aeolyus/ha-green-poe-scad/renders/front.png

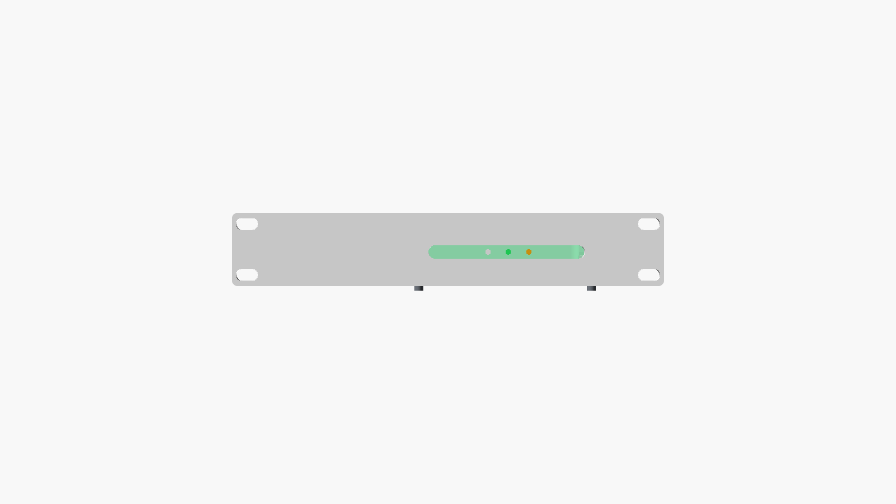
renders/front.png
