aeolyus/ha-green-poe-scad/renders/front_ethernet_far_right.png

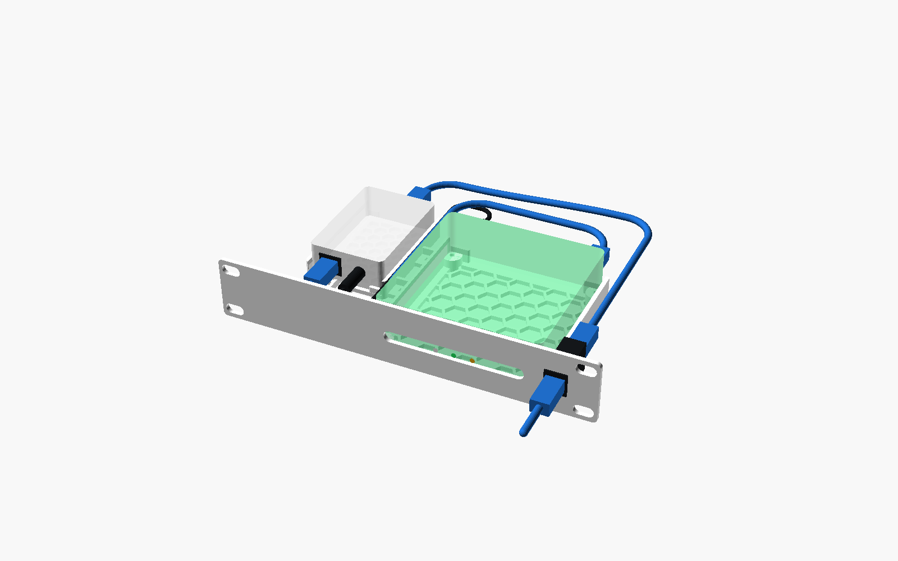
renders/front_ethernet_far_right.png
