aeolyus/ha-green-poe-scad/renders/x2d_plate.png

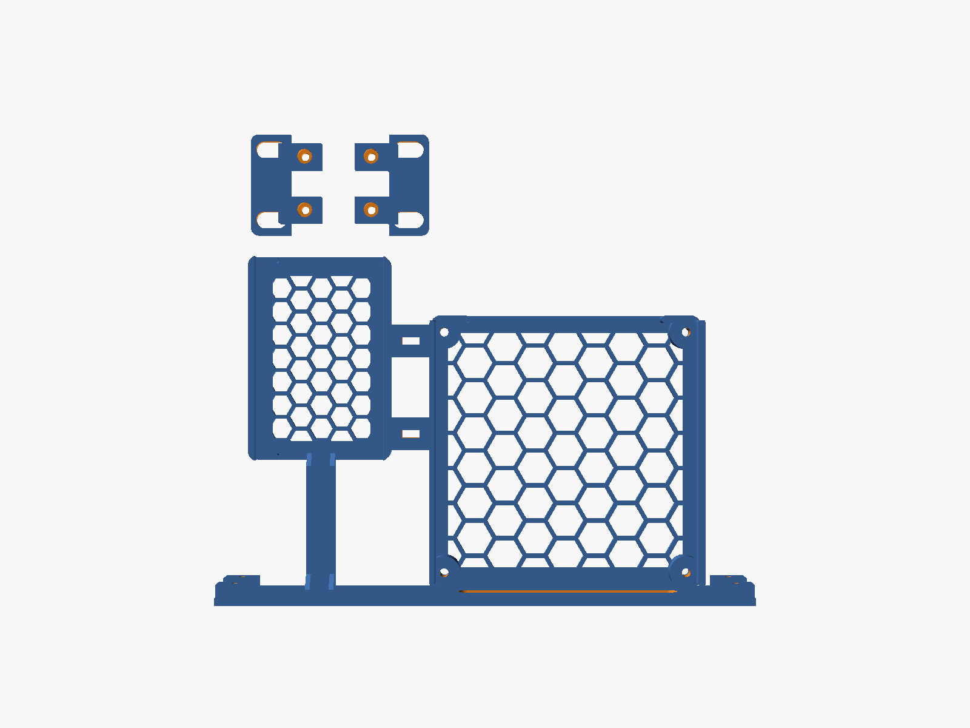
renders/x2d_plate.png
