aeolyus/ha-green-poe-scad/viewer/variants/stacked_center/viewer_led_activity.stl

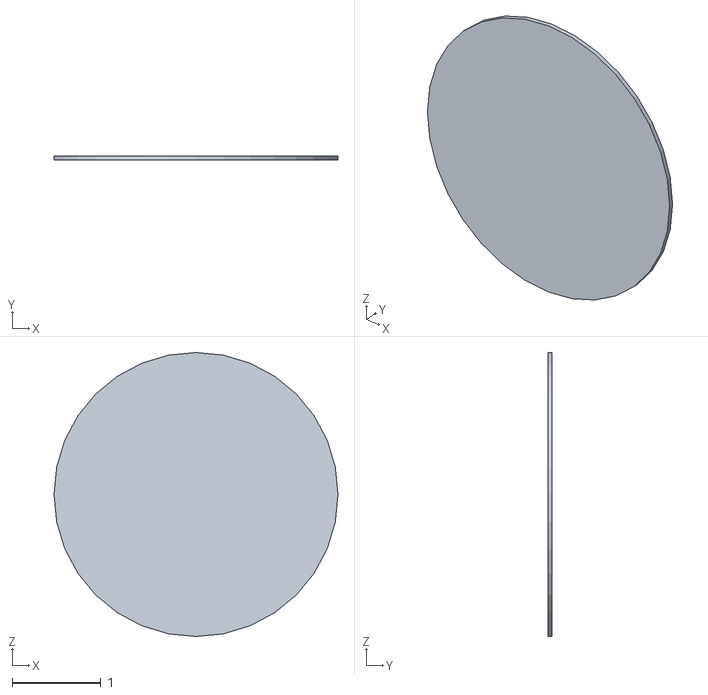
[picture p20: CAD file, 2026-08-29]
viewer/variants/stacked_center/viewer_led_activity.stl
3.20 x 0.05 x 3.20
