aeolyus/ha-green-poe-scad/viewer/viewer_retention_dovetail_gates.stl

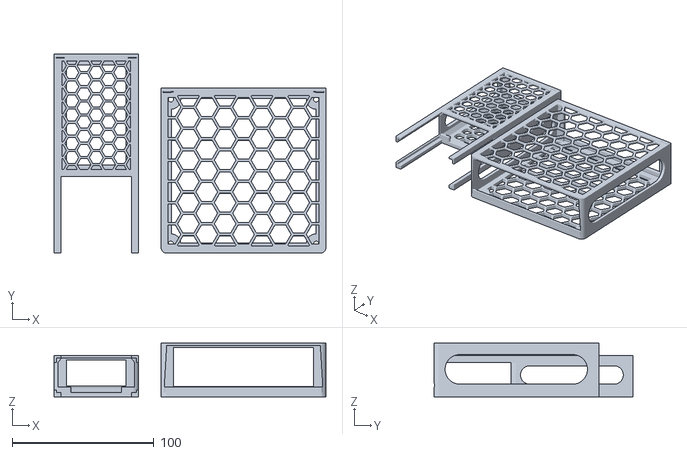
[picture p21: CAD file, 2026-08-29]
viewer/viewer_retention_dovetail_gates.stl
192.2 x 140.9 x 38.0
