aeolyus/ha-green-poe-scad/exports/one_piece_rear_cable_friendly_vent_frame_dovetail_ready.3mf

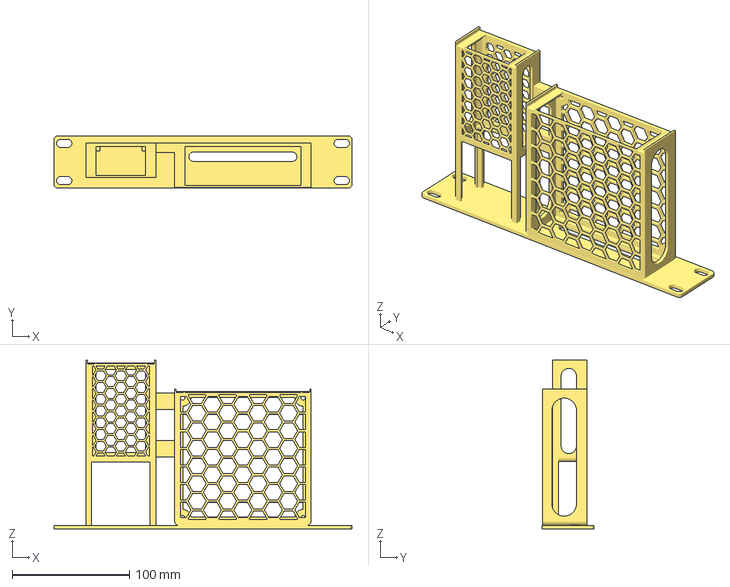
[picture p22: CAD file, 2026-08-29]
exports/one_piece_rear_cable_friendly_vent_frame_dovetail_ready.3mf
254.0 x 44.5 x 143.7 mm
