aeolyus/ha-green-poe-scad/viewer/variants/stacked_center/viewer_green_tray_friction_pads.stl

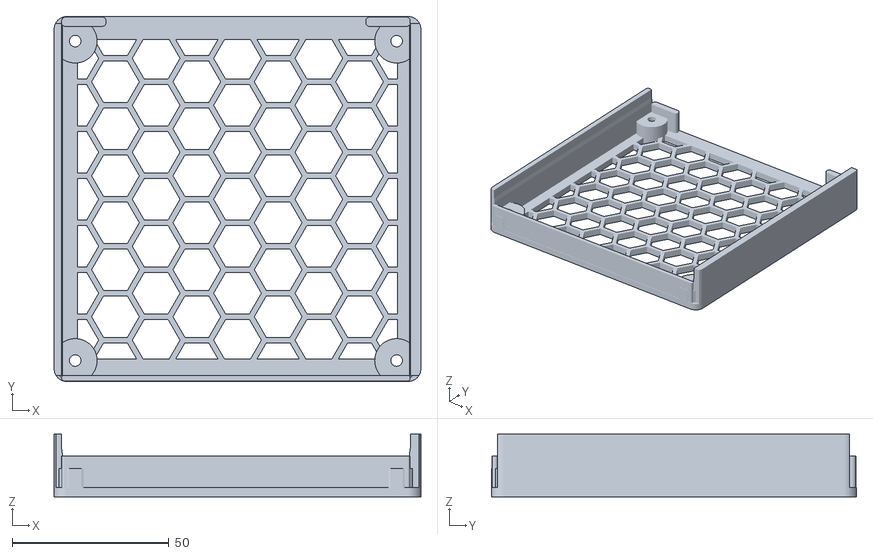
[picture p23: CAD file, 2026-08-29]
viewer/variants/stacked_center/viewer_green_tray_friction_pads.stl
117.1 x 116.6 x 20.0
