aeolyus/ha-green-poe-scad/viewer/variants/unified_roof/viewer_retention_ventilated_sleeves.stl

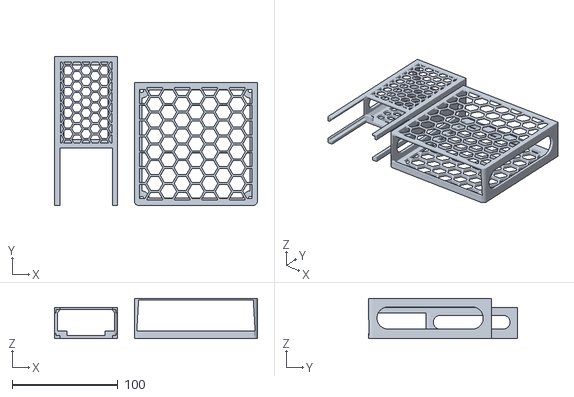
[picture p24: CAD file, 2026-08-29]
viewer/variants/unified_roof/viewer_retention_ventilated_sleeves.stl
192.2 x 140.9 x 38.0
