aeolyus/ha-green-poe-scad/viewer/viewer_green_tray_friction.stl

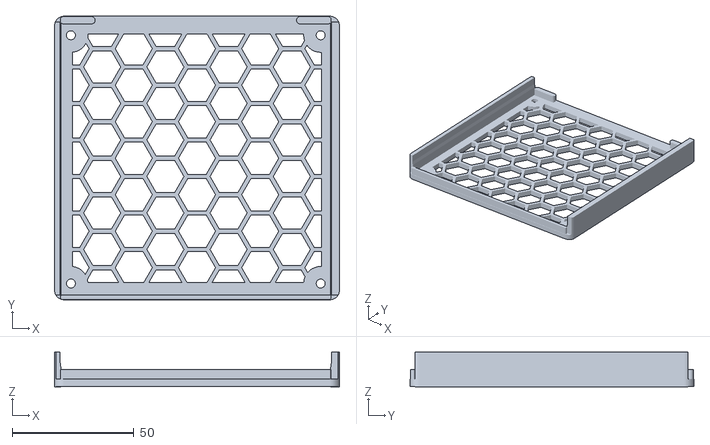
[picture p25: CAD file, 2026-08-29]
viewer/viewer_green_tray_friction.stl
117.1 x 116.6 x 14.2
