aeolyus/ha-green-poe-scad/viewer/variants/stacked_center/viewer_green_tray_friction_skeletal.stl

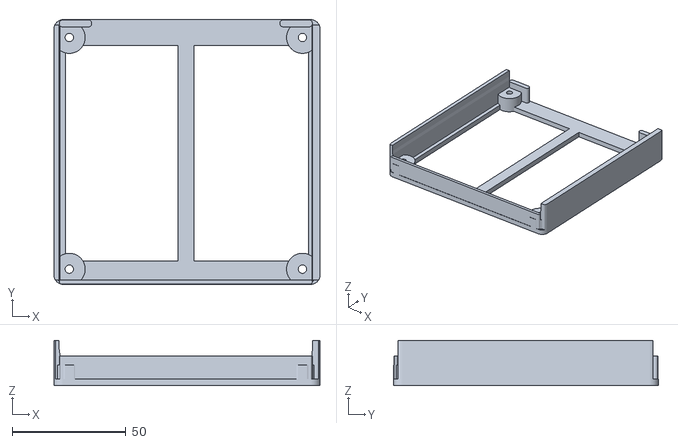
[picture p27: CAD file, 2026-08-29]
viewer/variants/stacked_center/viewer_green_tray_friction_skeletal.stl
117.1 x 116.6 x 20.0
