aeolyus/ha-green-poe-scad/exports/x2d_plate_rear_cable_friendly_vent_frame_no_dovetail.3mf

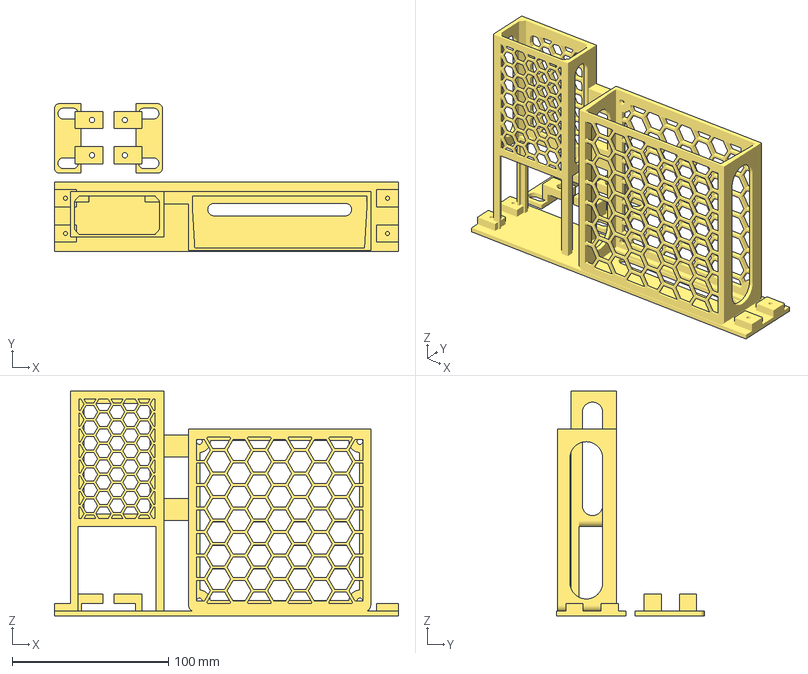
[picture p28: CAD file, 2026-08-29]
exports/x2d_plate_rear_cable_friendly_vent_frame_no_dovetail.3mf
220.0 x 94.5 x 143.7 mm
