aeolyus/ha-green-poe-scad/viewer/variants/stacked_center/viewer_mount_without_green_tray_no_shutter.stl

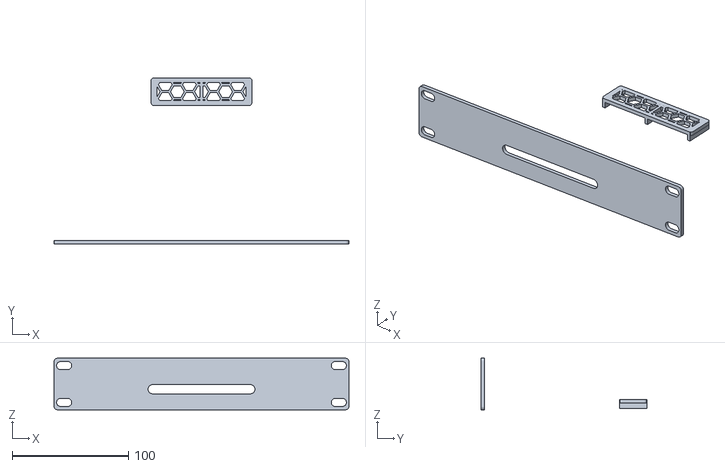
[picture p29: CAD file, 2026-08-29]
viewer/variants/stacked_center/viewer_mount_without_green_tray_no_shutter.stl
254.0 x 142.9 x 44.5
