aeolyus/ha-green-poe-scad/viewer/variants/unified_roof/viewer_mount_without_green_tray_no_shutter.stl

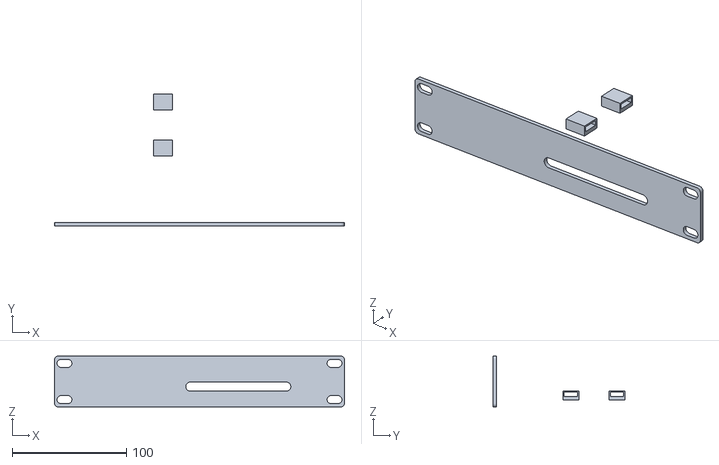
[picture p30: CAD file, 2026-08-29]
viewer/variants/unified_roof/viewer_mount_without_green_tray_no_shutter.stl
254.0 x 115.6 x 44.5
