aeolyus/ha-green-poe-scad/exports/dovetail_gates_optional_plate.3mf

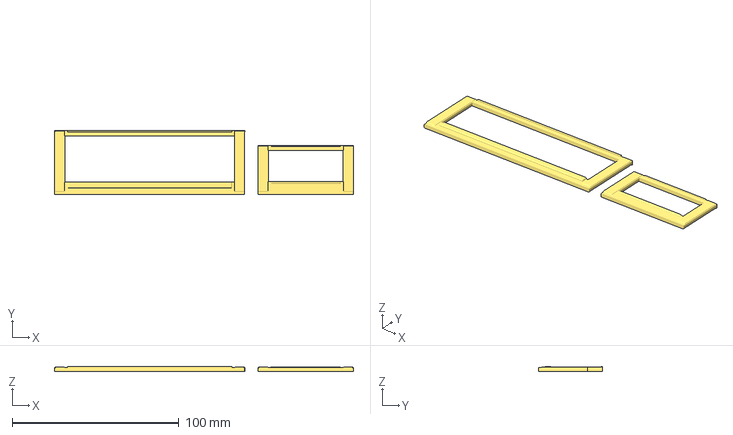
[picture p31: CAD file, 2026-08-29]
exports/dovetail_gates_optional_plate.3mf
179.1 x 38.0 x 3.28 mm
