aeolyus/ha-green-poe-scad/viewer/variants/stacked_center/viewer_shutter_open.stl

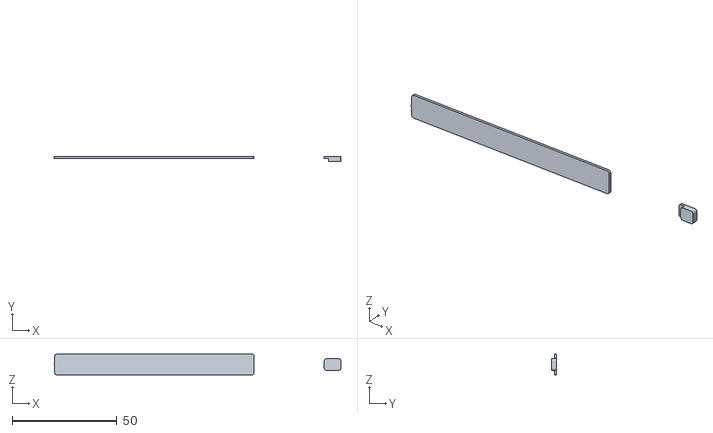
[picture p32: CAD file, 2026-08-29]
viewer/variants/stacked_center/viewer_shutter_open.stl
136.8 x 2.40 x 10.0
