aeolyus/ha-green-poe-scad/exports/splitter_vent_frame_coupon.3mf

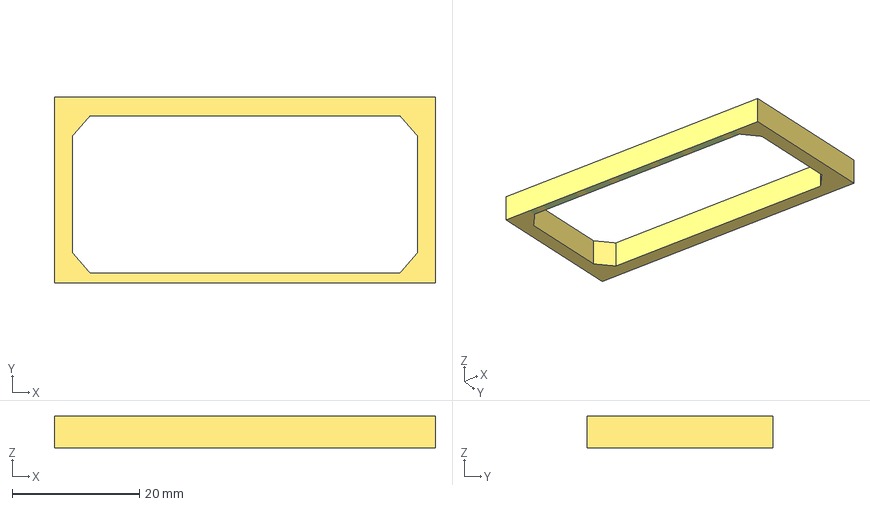
[picture p33: CAD file, 2026-08-29]
exports/splitter_vent_frame_coupon.3mf
59.8 x 29.3 x 5.00 mm
