aeolyus/ha-green-poe-scad/viewer/variants/unified_roof/viewer_insert.stl

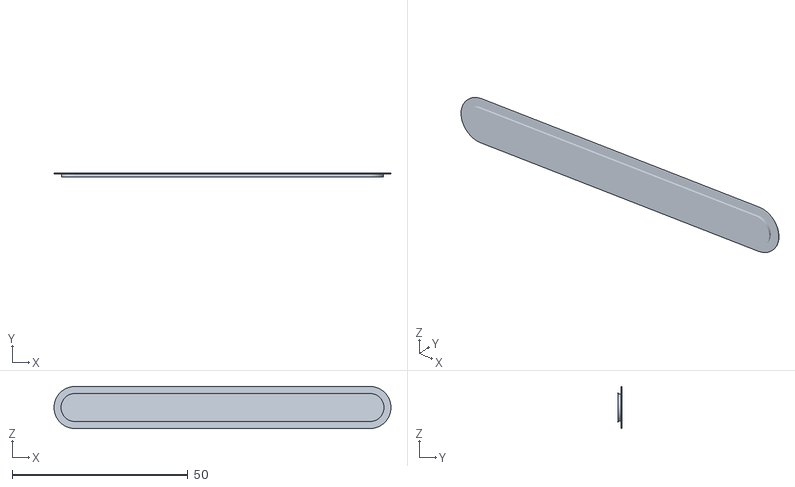
[picture p34: CAD file, 2026-08-29]
viewer/variants/unified_roof/viewer_insert.stl
96.0 x 1.20 x 12.0
