aeolyus/ha-green-poe-scad/viewer/viewer_green_tray_standard.stl

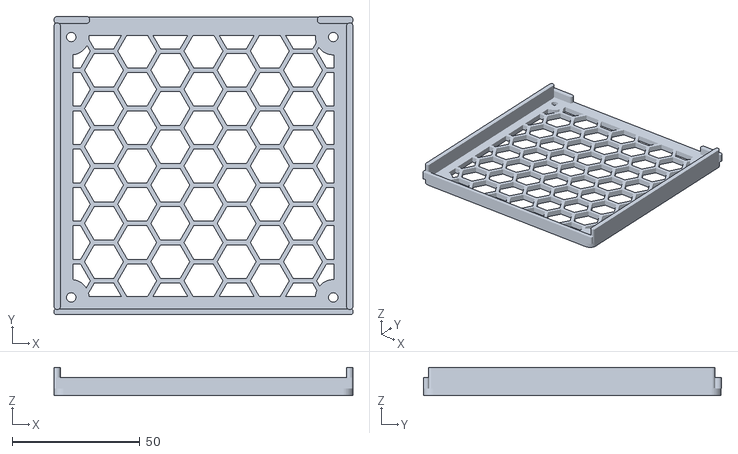
[picture p35: CAD file, 2026-08-29]
viewer/viewer_green_tray_standard.stl
117.1 x 116.8 x 11.0
