aeolyus/ha-green-poe-scad/exports/green_vent_frame_coupon.3mf

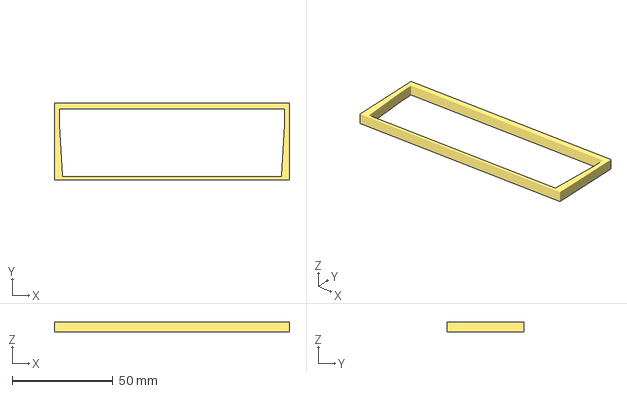
[picture p36: CAD file, 2026-08-29]
exports/green_vent_frame_coupon.3mf
116.5 x 38.0 x 5.00 mm
