aeolyus/ha-green-poe-scad/viewer/variants/unified_roof/viewer_shutter_retainer.stl

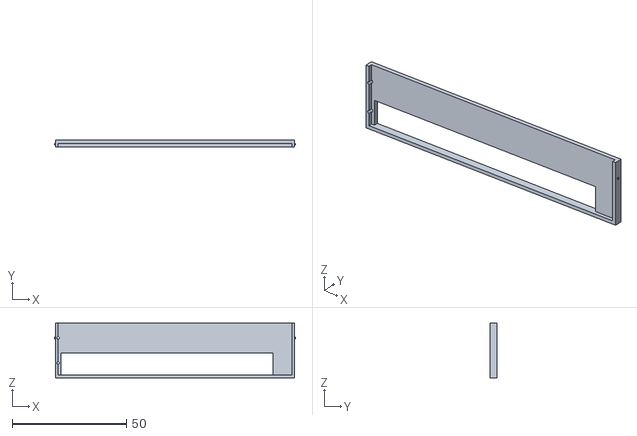
[picture p37: CAD file, 2026-08-29]
viewer/variants/unified_roof/viewer_shutter_retainer.stl
105.7 x 2.90 x 24.0
