aeolyus/ha-green-poe-scad/exports/vent_frame_coupon.3mf

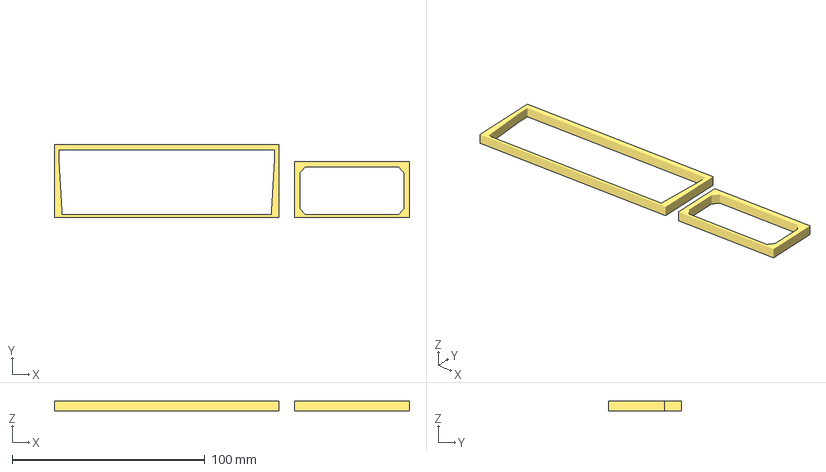
[picture p38: CAD file, 2026-08-29]
exports/vent_frame_coupon.3mf
184.3 x 38.0 x 5.00 mm
