aeolyus/ha-green-poe-scad/viewer/variants/unified_roof/viewer_shutter_open.stl

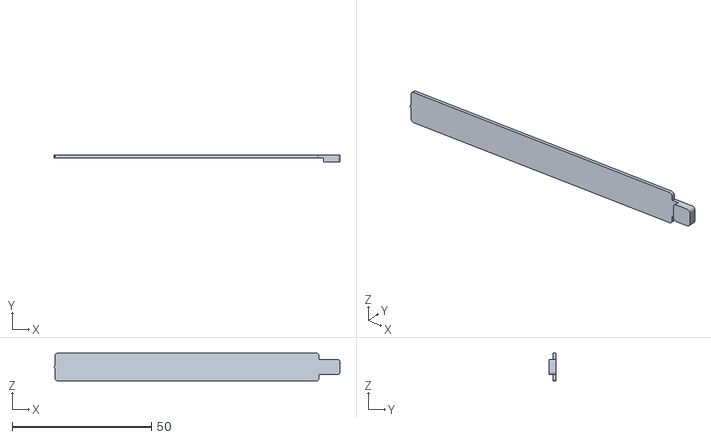
[picture p39: CAD file, 2026-08-29]
viewer/variants/unified_roof/viewer_shutter_open.stl
102.8 x 2.40 x 10.0
