aeolyus/ha-green-poe-scad/exports/dovetail_rail_coupon.3mf

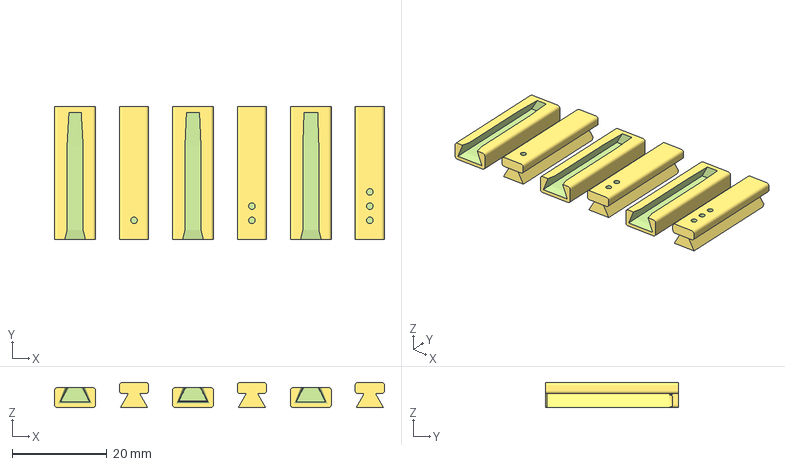
[picture p40: CAD file, 2026-08-28]
exports/dovetail_rail_coupon.3mf
69.7 x 28.0 x 5.35 mm
