aeolyus/ha-green-poe-scad/viewer/viewer_green_ports.stl

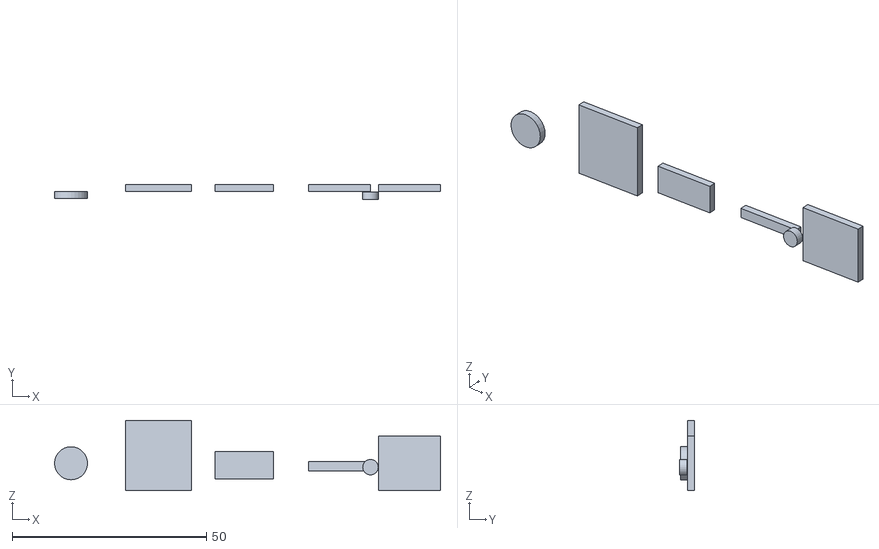
[picture p41: CAD file, 2026-08-27]
viewer/viewer_green_ports.stl
99.2 x 3.90 x 18.0
