aeolyus/ha-green-poe-scad/exports/friction_fit_coupon.3mf

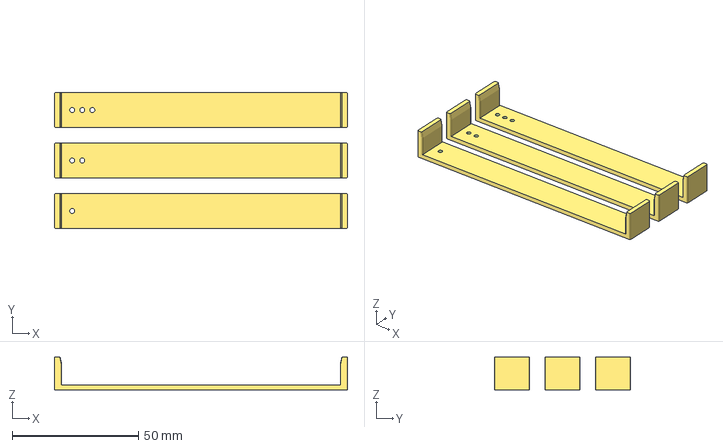
[picture p42: CAD file, 2026-08-28]
exports/friction_fit_coupon.3mf
116.1 x 54.0 x 13.0 mm
