aeolyus/ha-green-poe-scad/viewer/viewer_retention_x_cage.stl

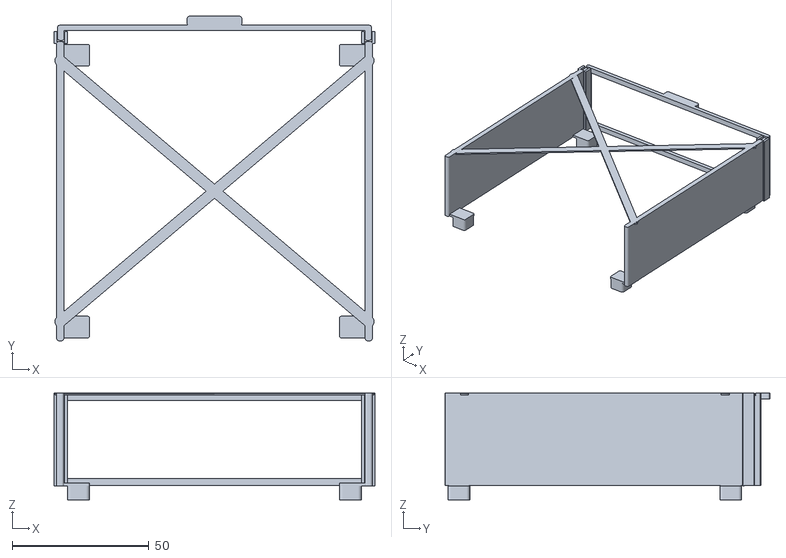
[picture p43: CAD file, 2026-08-27]
viewer/viewer_retention_x_cage.stl
117.5 x 118.8 x 39.1
