aeolyus/ha-green-poe-scad/exports/hybrid_clip_coupon.3mf

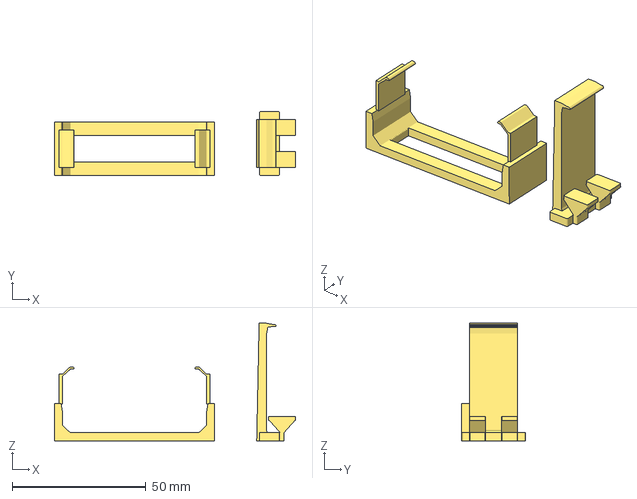
[picture p44: CAD file, 2026-08-28]
exports/hybrid_clip_coupon.3mf
90.0 x 24.0 x 43.9 mm
