aeolyus/ha-green-poe-scad/exports/fit_test.3mf

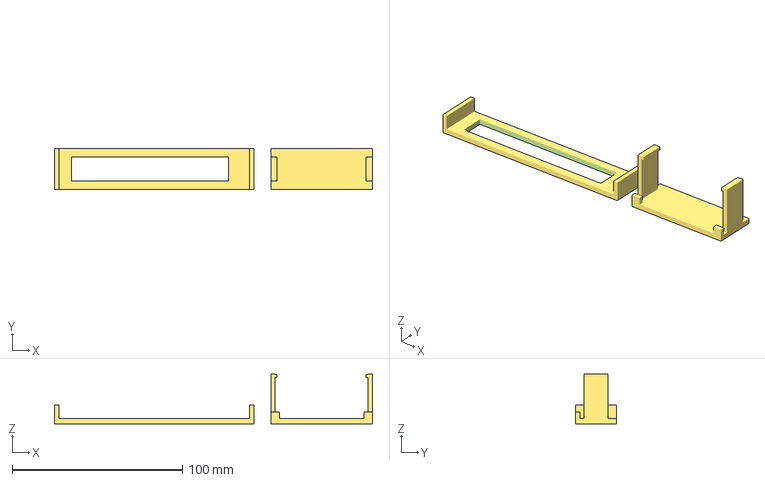
[picture p45: CAD file, 2026-08-28]
exports/fit_test.3mf
186.9 x 24.0 x 29.2 mm
