aeolyus/ha-green-poe-scad/viewer/variants/front_ethernet_left/viewer_keystone_ports.stl

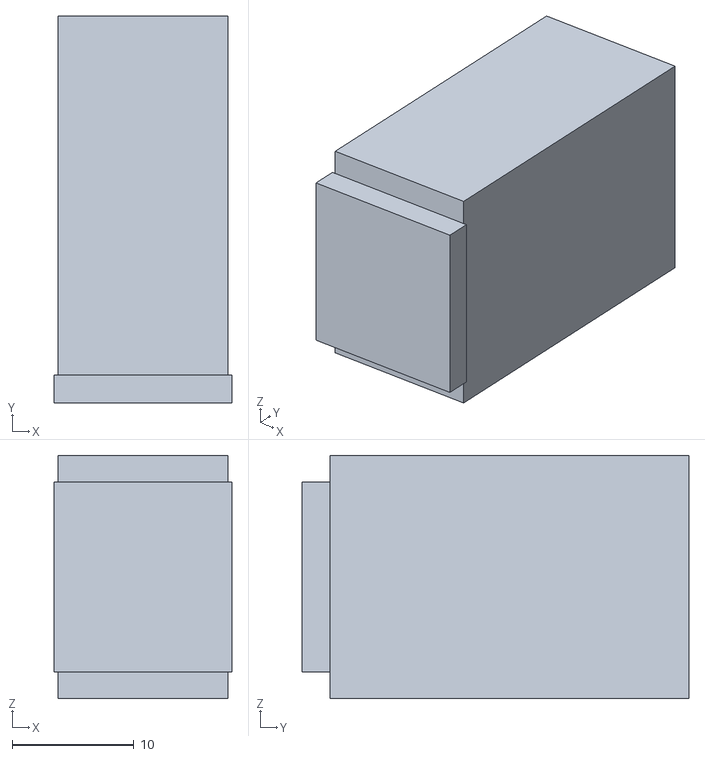
[picture p46: CAD file, 2026-08-28]
viewer/variants/front_ethernet_left/viewer_keystone_ports.stl
14.6 x 31.8 x 20.0
