aeolyus/ha-green-poe-scad/exports/green_hybrid_clip_coupon.3mf

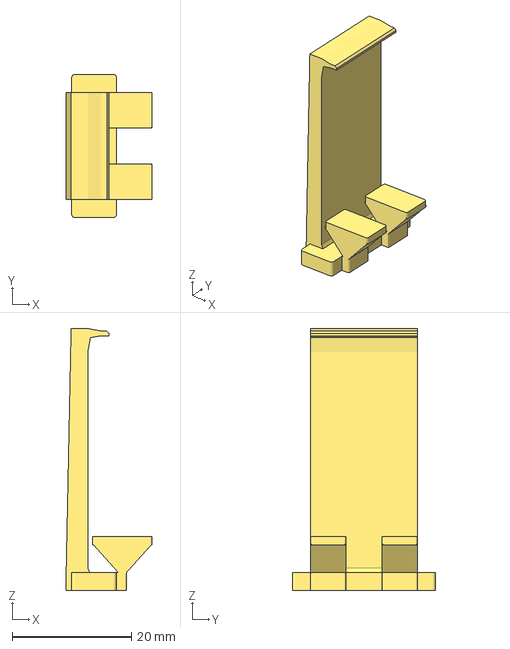
[picture p47: CAD file, 2026-08-28]
exports/green_hybrid_clip_coupon.3mf
14.5 x 24.0 x 43.9 mm
