aeolyus/ha-green-poe-scad/viewer/variants/unified_roof/viewer_splitter.stl

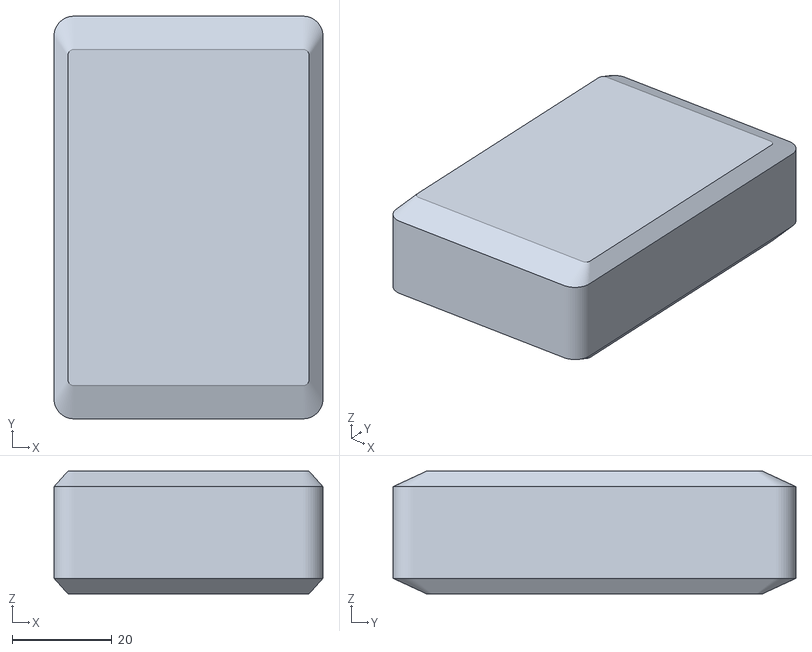
[picture p48: CAD file, 2026-08-28]
viewer/variants/unified_roof/viewer_splitter.stl
54.0 x 80.8 x 24.6
