aeolyus/ha-green-poe-scad/viewer/viewer_retention_padded_rails.stl

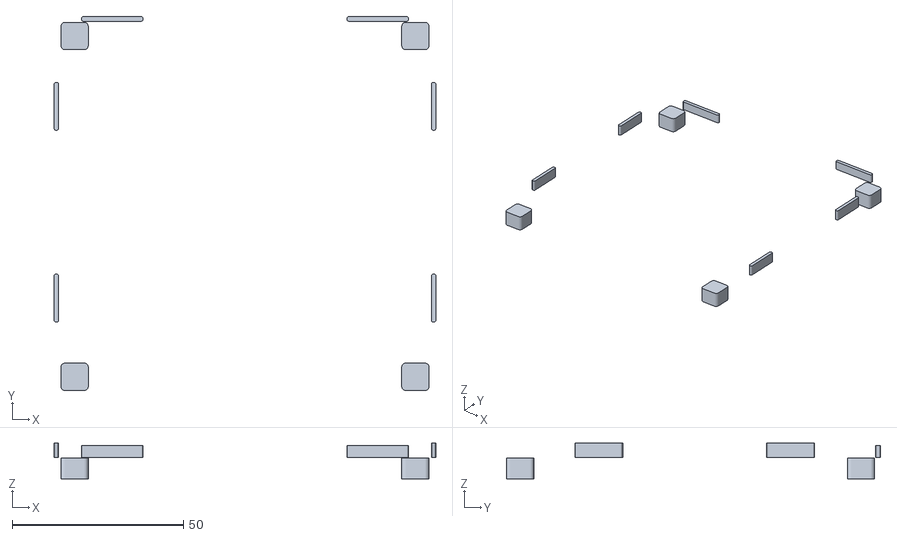
[picture p49: CAD file, 2026-08-27]
viewer/viewer_retention_padded_rails.stl
111.5 x 109.2 x 10.4
