aeolyus/ha-green-poe-scad/exports/x2d_plate.3mf

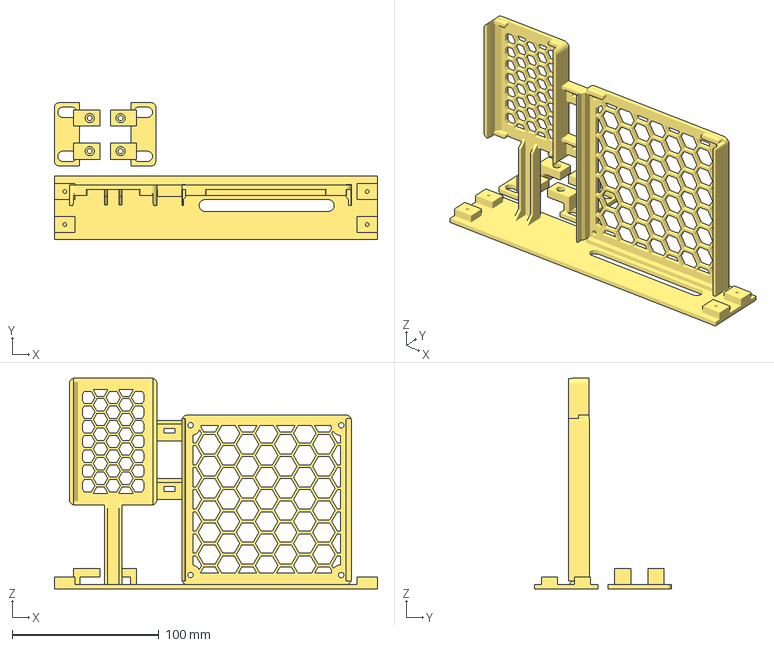
[picture p50: CAD file, 2026-08-28]
exports/x2d_plate.3mf
220.0 x 93.0 x 143.7 mm
