aeolyus/ha-green-poe-scad/viewer/variants/unified_roof/viewer_dc_cable.stl

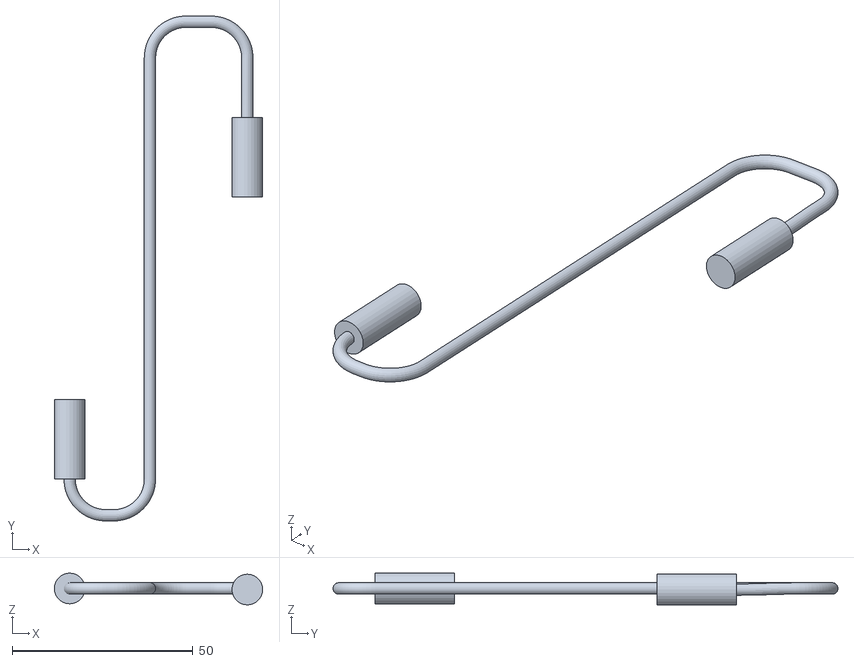
[picture p51: CAD file, 2026-08-28]
viewer/variants/unified_roof/viewer_dc_cable.stl
57.6 x 139.7 x 8.80
