aeolyus/ha-green-poe-scad/viewer/viewer_retention_friction_sleeve.stl

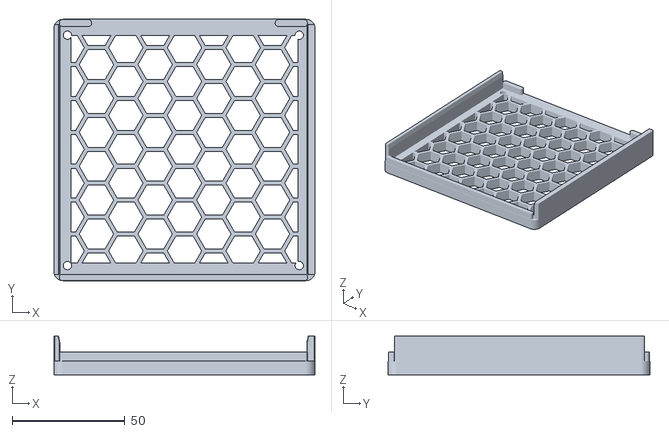
[picture p52: CAD file, 2026-08-27]
viewer/viewer_retention_friction_sleeve.stl
115.5 x 115.8 x 17.2
