aeolyus/ha-green-poe-scad/exports/one_piece.3mf

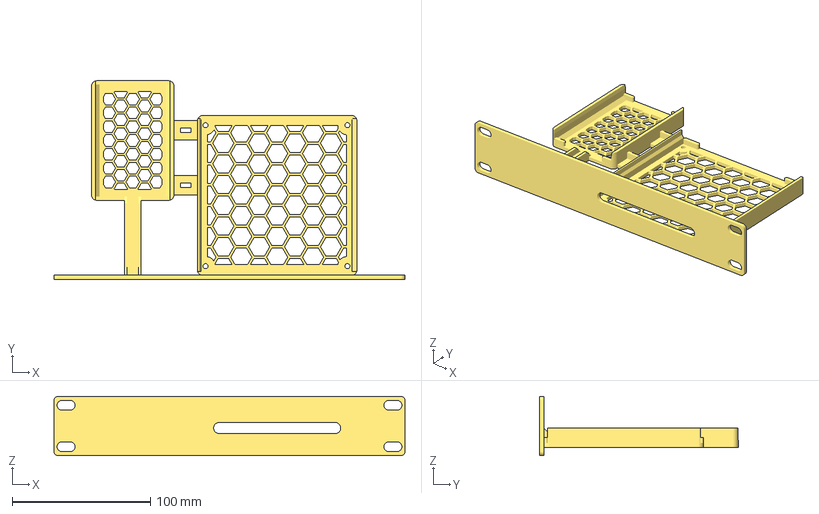
[picture p53: CAD file, 2026-08-28]
exports/one_piece.3mf
254.0 x 143.7 x 43.0 mm
