aeolyus/ha-green-poe-scad/viewer/variants/stacked_center/viewer_retention_hybrid_clips.stl

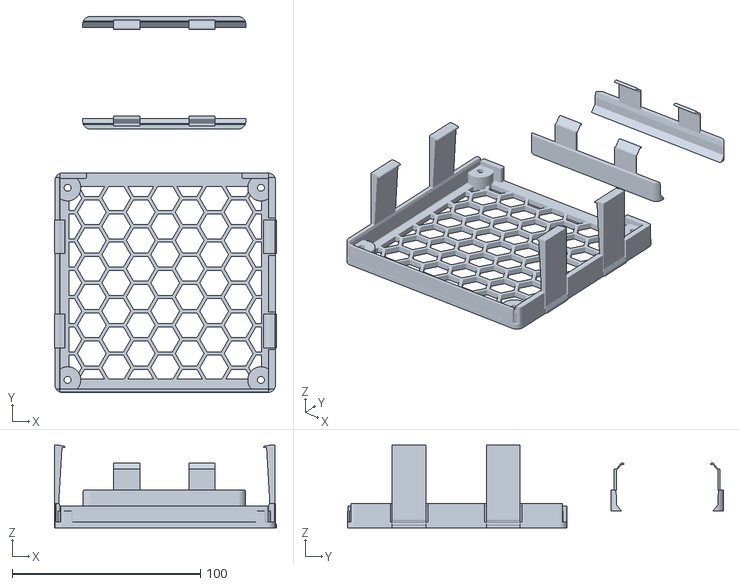
[picture p54: CAD file, 2026-08-29]
viewer/variants/stacked_center/viewer_retention_hybrid_clips.stl
117.9 x 199.6 x 43.9
