aeolyus/ha-green-poe-scad/viewer/variants/unified_roof/viewer_splitter_side_walls.stl

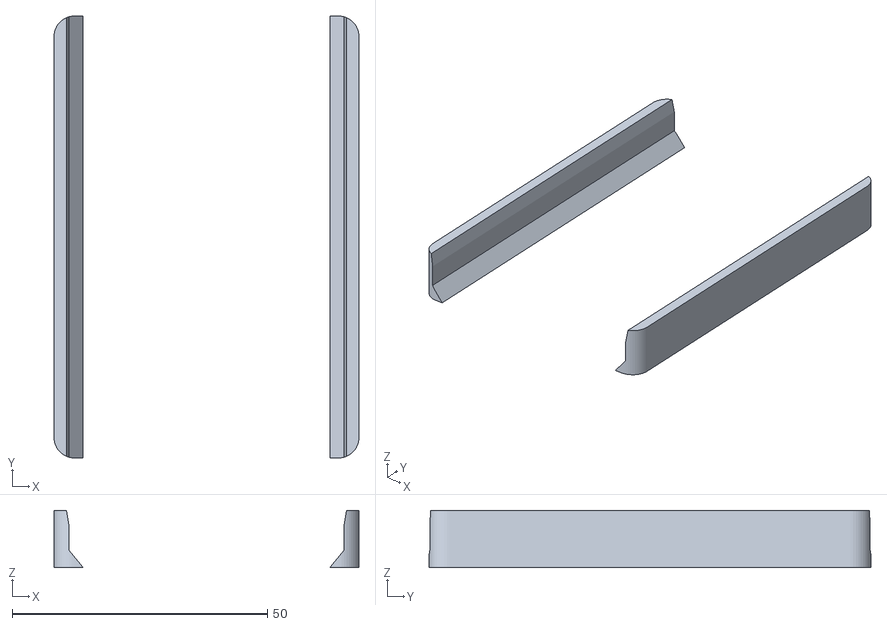
[picture p55: CAD file, 2026-08-28]
viewer/variants/unified_roof/viewer_splitter_side_walls.stl
59.8 x 86.6 x 11.2
