aeolyus/ha-green-poe-scad/viewer/viewer_ports.stl

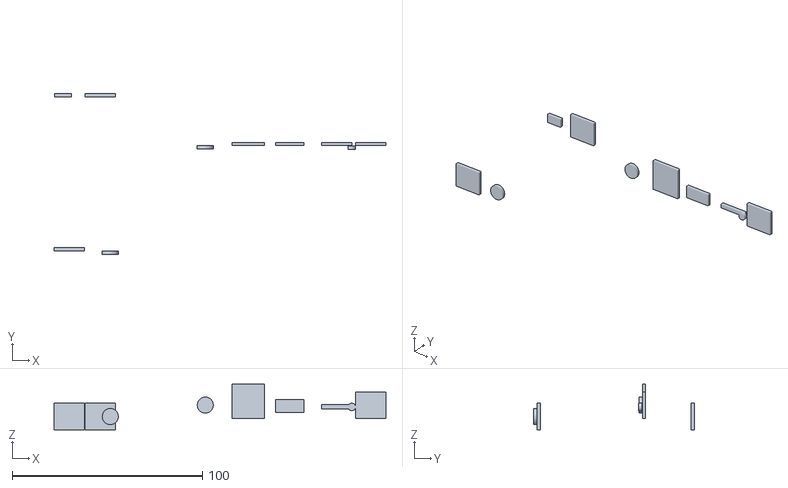
[picture p56: CAD file, 2026-08-27]
viewer/viewer_ports.stl
174.5 x 84.4 x 24.0
