aeolyus/ha-green-poe-scad/viewer/variants/unified_roof/viewer_input_data_cable.stl

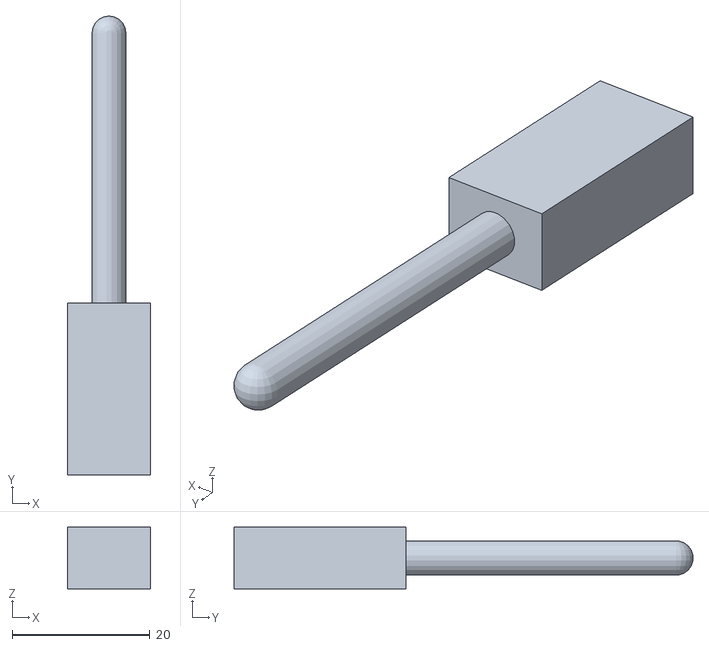
[picture p57: CAD file, 2026-08-28]
viewer/variants/unified_roof/viewer_input_data_cable.stl
12.0 x 66.7 x 9.00
