aeolyus/ha-green-poe-scad/exports/core.stl

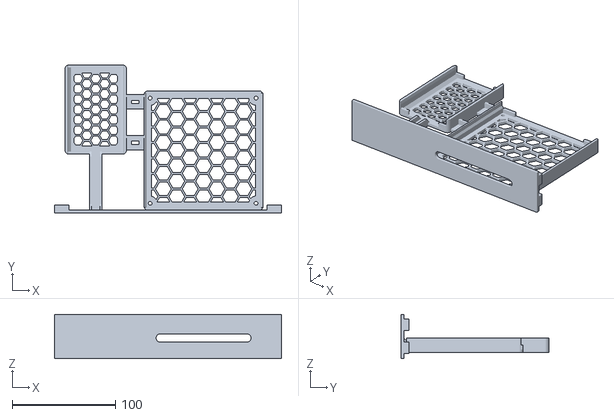
[picture p58: CAD file, 2026-08-28]
exports/core.stl
220.0 x 143.7 x 43.0
