aeolyus/ha-green-poe-scad/viewer/variants/stacked_center/viewer_dc_cable.stl

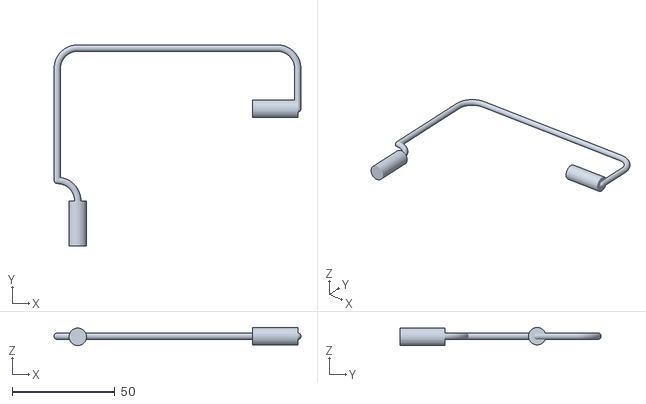
[picture p59: CAD file, 2026-08-28]
viewer/variants/stacked_center/viewer_dc_cable.stl
120.1 x 98.0 x 8.80
