aeolyus/ha-green-poe-scad/viewer/variants/unified_roof/viewer_splitter_ports.stl

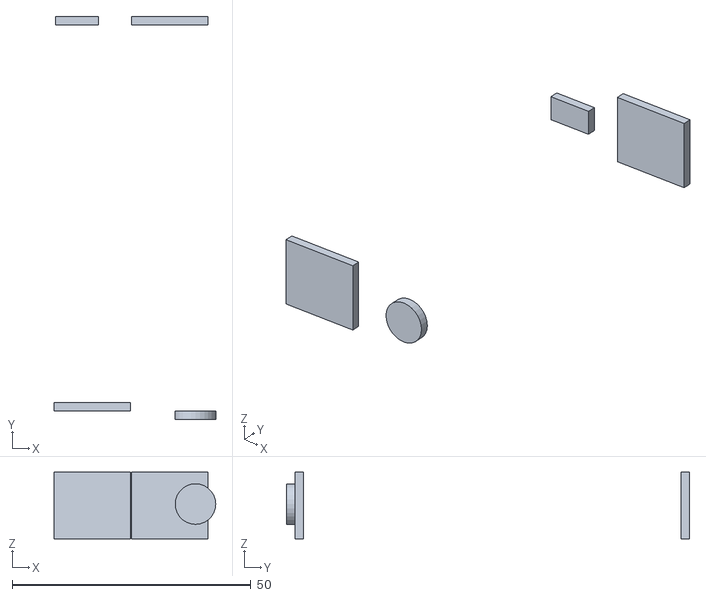
[picture p60: CAD file, 2026-08-28]
viewer/variants/unified_roof/viewer_splitter_ports.stl
33.9 x 84.4 x 14.0
