aeolyus/ha-green-poe-scad/exports/splitter_hybrid_clip_coupon.3mf

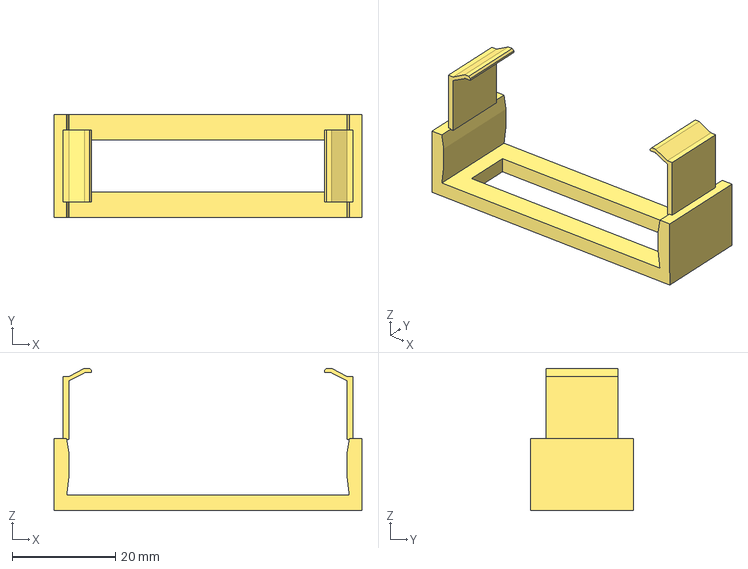
[picture p61: CAD file, 2026-08-28]
exports/splitter_hybrid_clip_coupon.3mf
59.8 x 20.0 x 27.6 mm
