aeolyus/ha-green-poe-scad/viewer/variants/unified_roof/viewer_internal_data_cable.stl

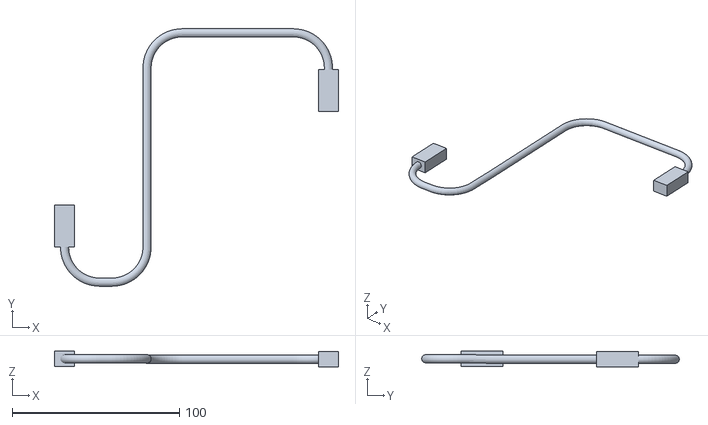
[picture p62: CAD file, 2026-08-28]
viewer/variants/unified_roof/viewer_internal_data_cable.stl
169.7 x 153.9 x 9.30
