aeolyus/ha-green-poe-scad/viewer/viewer_retention_corner_gate.stl

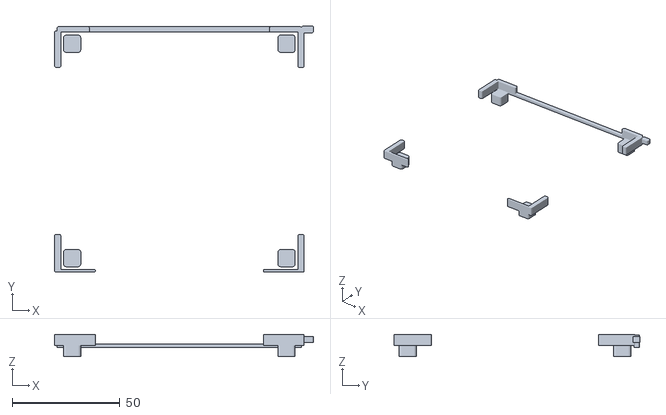
[picture p63: CAD file, 2026-08-27]
viewer/viewer_retention_corner_gate.stl
120.2 x 114.3 x 10.3
