aeolyus/ha-green-poe-scad/exports/splitter_fit_coupon.3mf

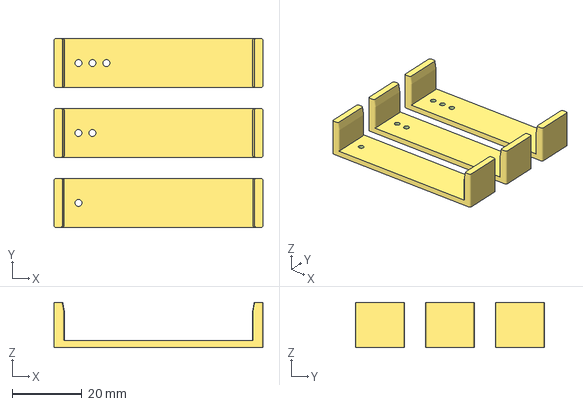
[picture p64: CAD file, 2026-08-28]
exports/splitter_fit_coupon.3mf
59.8 x 54.0 x 13.0 mm
