aeolyus/ha-green-poe-scad/viewer/variants/stacked_center/viewer_internal_data_cable.stl

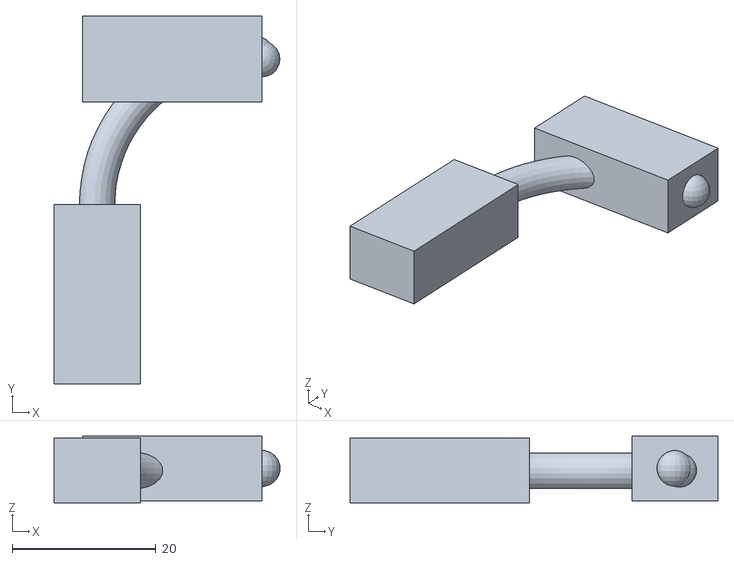
[picture p65: CAD file, 2026-08-28]
viewer/variants/stacked_center/viewer_internal_data_cable.stl
31.4 x 51.2 x 9.30
