aeolyus/ha-green-poe-scad/viewer/variants/unified_roof/viewer_green.stl

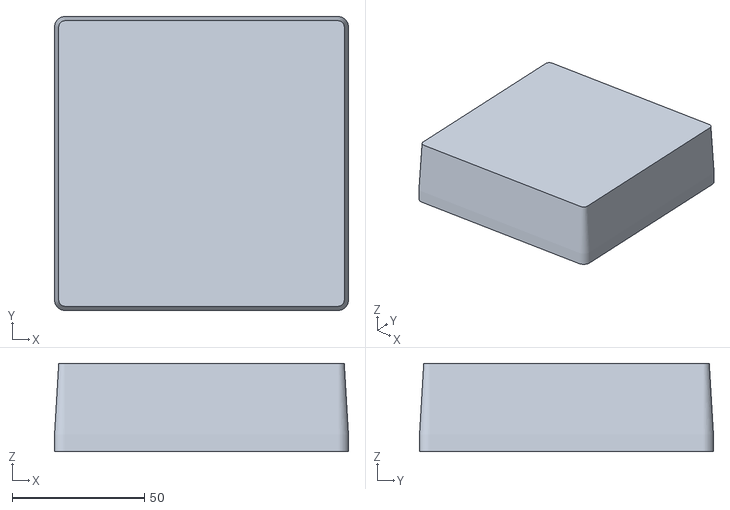
[picture p66: CAD file, 2026-08-28]
viewer/variants/unified_roof/viewer_green.stl
111.1 x 111.1 x 33.3
