aeolyus/ha-green-poe-scad/viewer/viewer_retention_captive_strap.stl

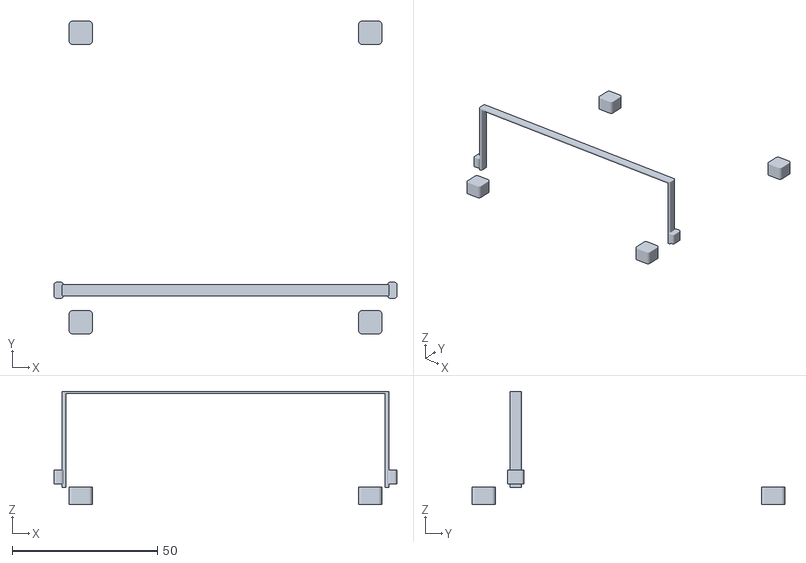
[picture p67: CAD file, 2026-08-27]
viewer/viewer_retention_captive_strap.stl
117.9 x 107.5 x 38.9
