aeolyus/ha-green-poe-scad/exports/core_front_ethernet_left.stl

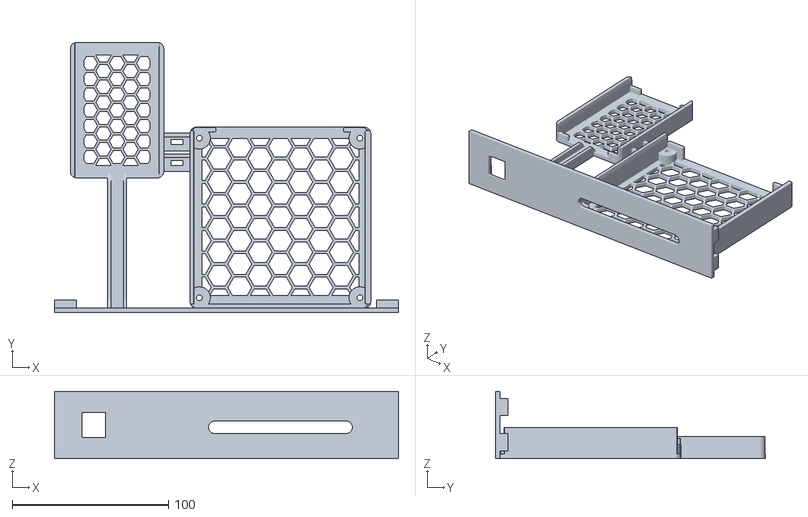
[picture p68: CAD file, 2026-08-27]
exports/core_front_ethernet_left.stl
220.0 x 172.7 x 43.0
