aeolyus/ha-green-poe-scad/viewer/variants/stacked_center/viewer_input_data_cable.stl

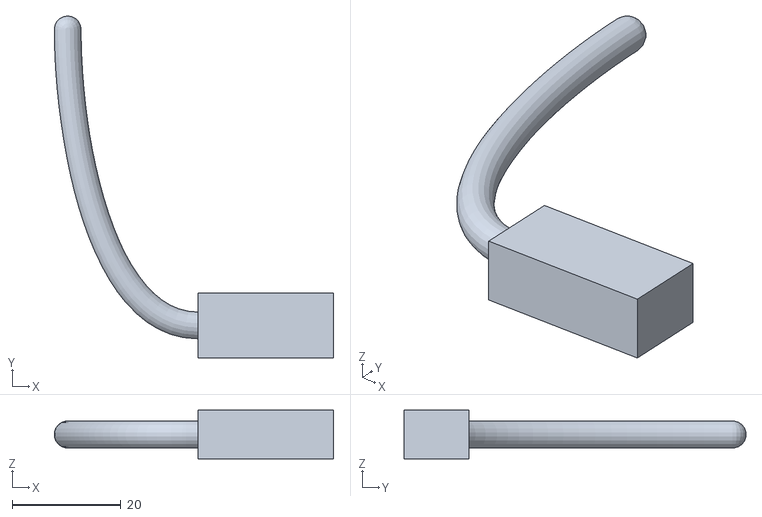
[picture p69: CAD file, 2026-08-28]
viewer/variants/stacked_center/viewer_input_data_cable.stl
51.5 x 63.0 x 9.00
