aeolyus/ha-green-poe-scad/viewer/variants/unified_roof/viewer_enclosure_airframe.stl

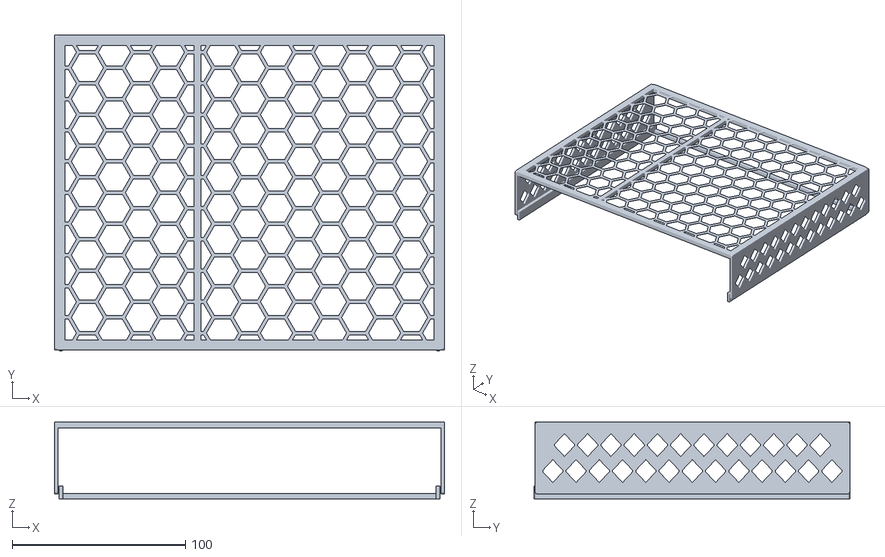
[picture p70: CAD file, 2026-08-28]
viewer/variants/unified_roof/viewer_enclosure_airframe.stl
225.0 x 182.2 x 44.2
