aeolyus/ha-green-poe-scad/viewer/variants/stacked_center/viewer_splitter_ports.stl

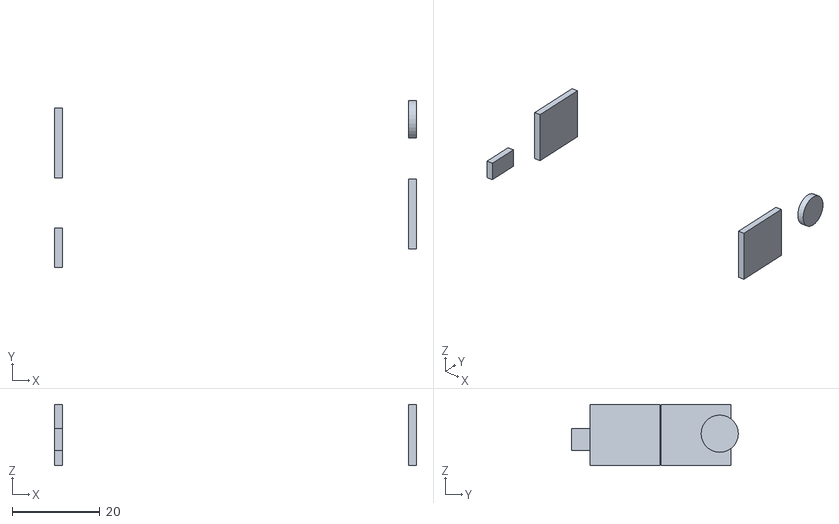
[picture p71: CAD file, 2026-08-28]
viewer/variants/stacked_center/viewer_splitter_ports.stl
82.6 x 38.0 x 14.0
