aeolyus/ha-green-poe-scad/viewer/variants/unified_roof/viewer_rulers.stl

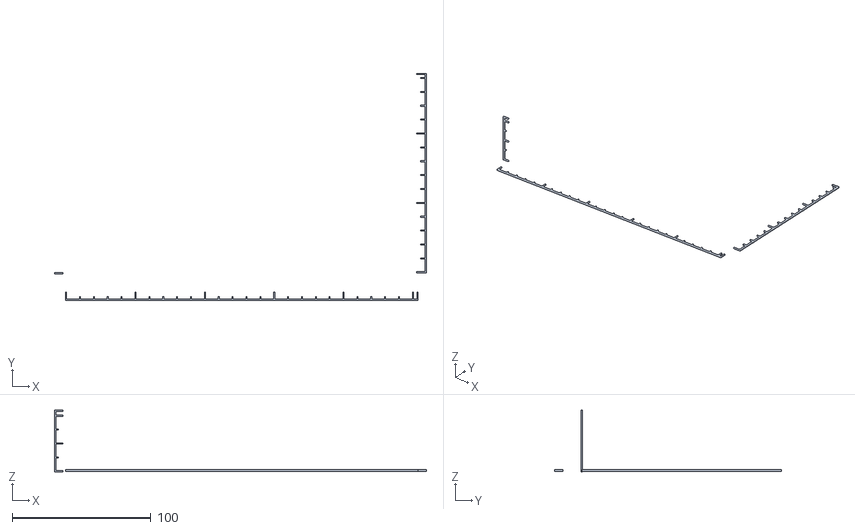
[picture p72: CAD file, 2026-08-28]
viewer/variants/unified_roof/viewer_rulers.stl
268.2 x 163.7 x 44.5
