aeolyus/ha-green-poe-scad/viewer/viewer_internal_data_cable.stl

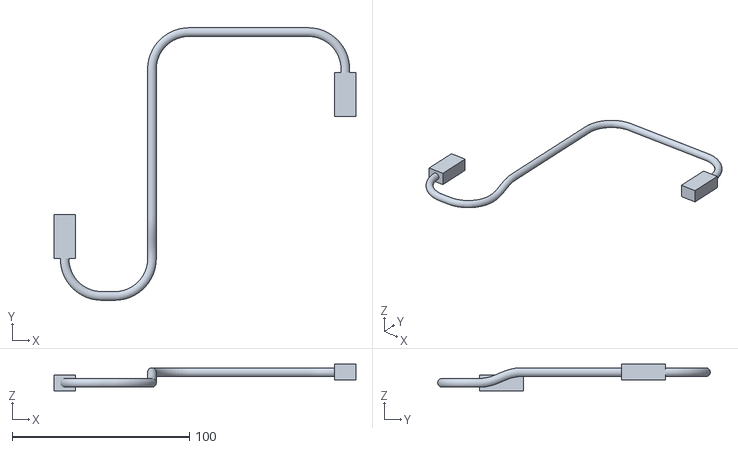
[picture p73: CAD file, 2026-08-27]
viewer/viewer_internal_data_cable.stl
170.5 x 153.9 x 15.0
