aeolyus/ha-green-poe-scad/viewer/variants/stacked_center/viewer_enclosure_airframe.stl

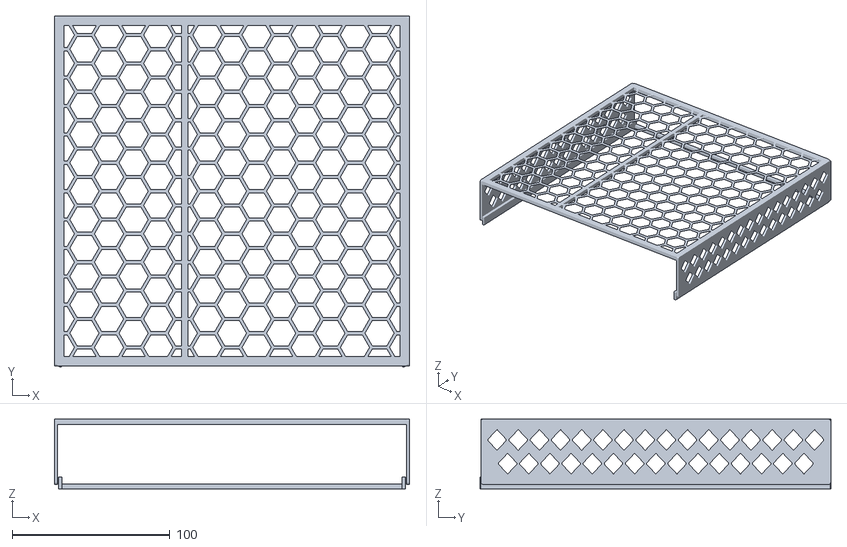
[picture p74: CAD file, 2026-08-28]
viewer/variants/stacked_center/viewer_enclosure_airframe.stl
225.0 x 222.2 x 44.2
