aeolyus/ha-green-poe-scad/viewer/viewer_green.stl

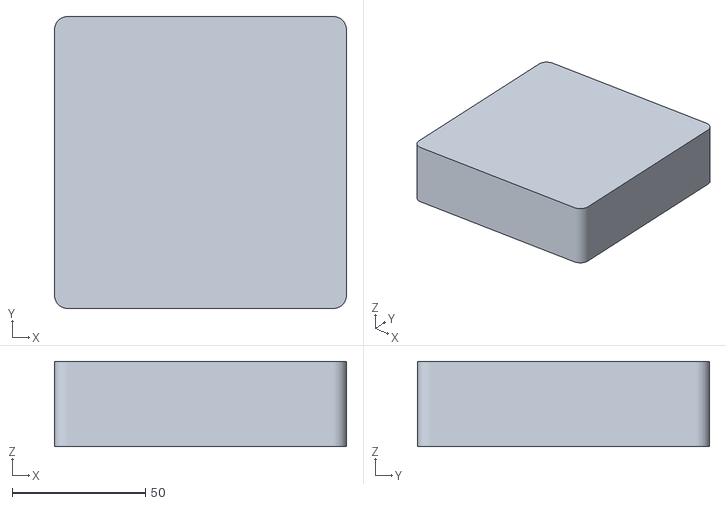
[picture p75: CAD file, 2026-08-27]
viewer/viewer_green.stl
109.5 x 109.5 x 32.0
