aeolyus/ha-green-poe-scad/exports/x2d_plate_with_logo.3mf

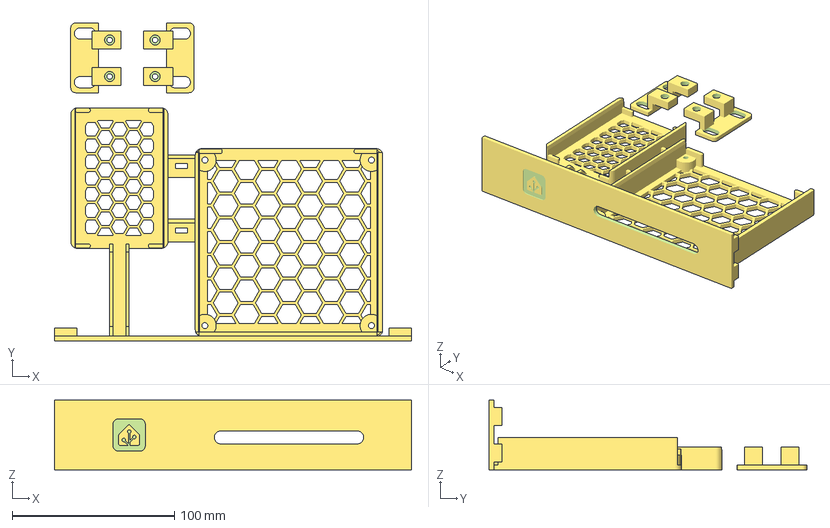
[picture p76: CAD file, 2026-08-27]
exports/x2d_plate_with_logo.3mf
220.0 x 196.0 x 43.0 mm
