aeolyus/ha-green-poe-scad/viewer/variants/stacked_center/viewer_rulers.stl

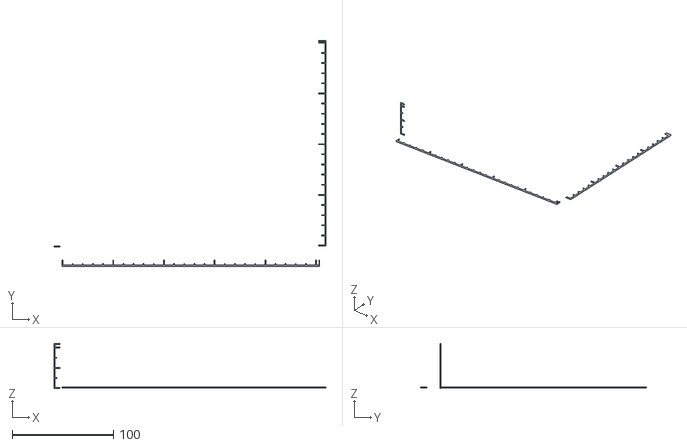
[picture p77: CAD file, 2026-08-28]
viewer/variants/stacked_center/viewer_rulers.stl
268.2 x 222.4 x 44.5
