aeolyus/ha-green-poe-scad/viewer/variants/unified_roof/viewer_splitter_floor.stl

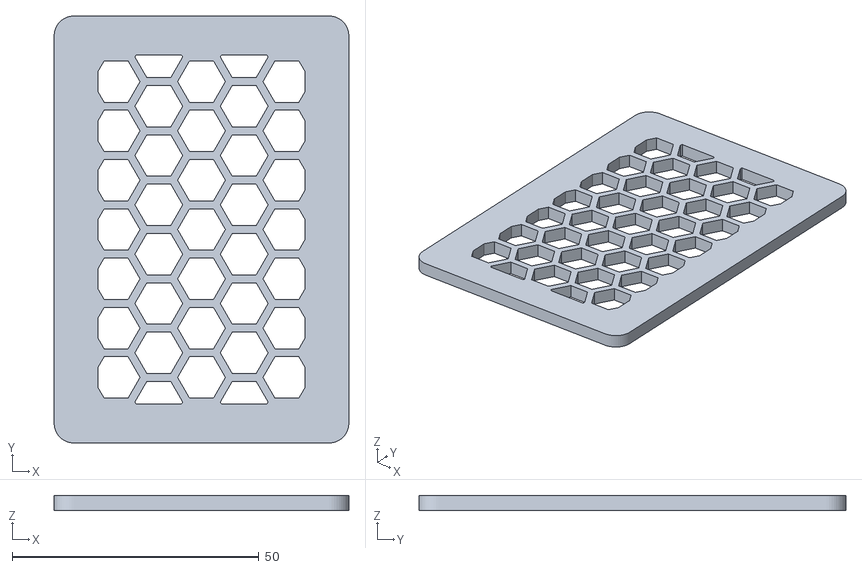
[picture p78: CAD file, 2026-08-28]
viewer/variants/unified_roof/viewer_splitter_floor.stl
59.8 x 86.6 x 3.00
