aeolyus/ha-green-poe-scad/viewer/viewer_retention_sled_gate.stl

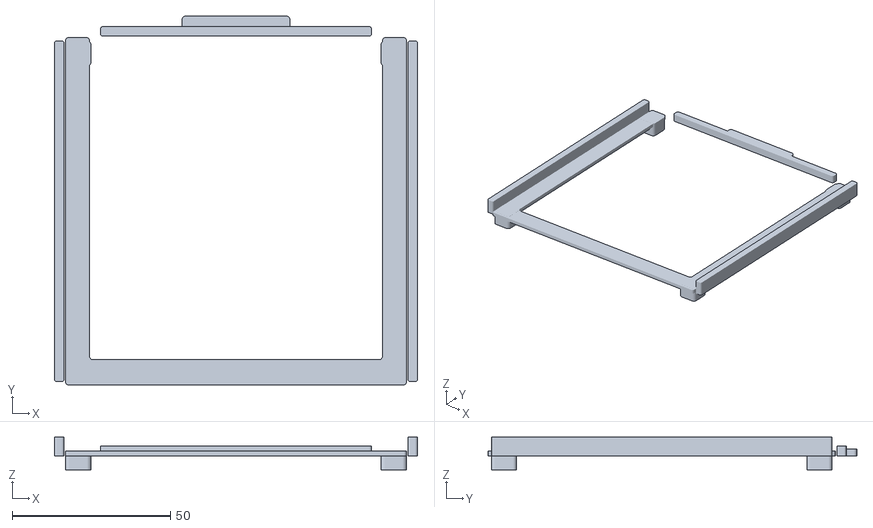
[picture p79: CAD file, 2026-08-27]
viewer/viewer_retention_sled_gate.stl
114.5 x 116.3 x 10.4
