aeolyus/ha-green-poe-scad/viewer/variants/unified_roof/viewer_splitter_end_stops.stl

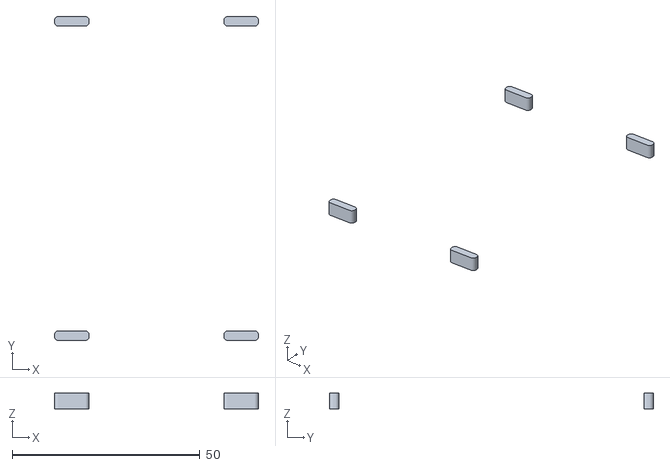
[picture p80: CAD file, 2026-08-28]
viewer/variants/unified_roof/viewer_splitter_end_stops.stl
54.3 x 86.2 x 4.20
