aeolyus/ha-green-poe-scad/viewer/variants/stacked_center/viewer_retention_slide_latch.stl

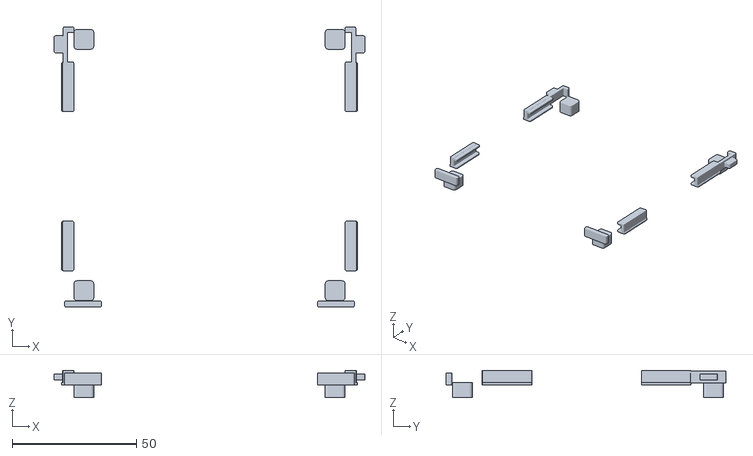
[picture p81: CAD file, 2026-08-28]
viewer/variants/stacked_center/viewer_retention_slide_latch.stl
125.1 x 112.7 x 11.0
