aeolyus/ha-green-poe-scad/viewer/variants/unified_roof/viewer_logo.stl

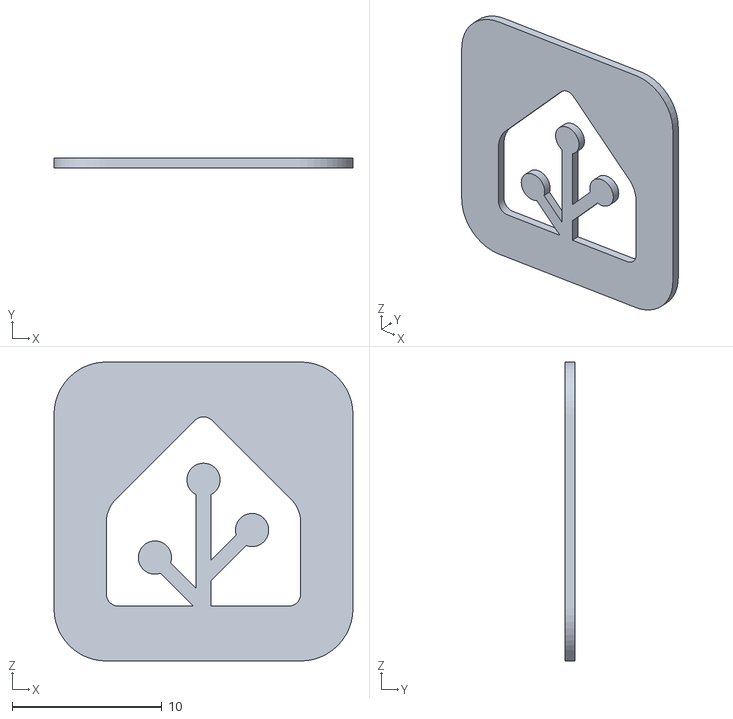
[picture p82: CAD file, 2026-08-27]
viewer/variants/unified_roof/viewer_logo.stl
20.0 x 0.66 x 20.0
