aeolyus/ha-green-poe-scad/viewer/viewer_dc_cable.stl

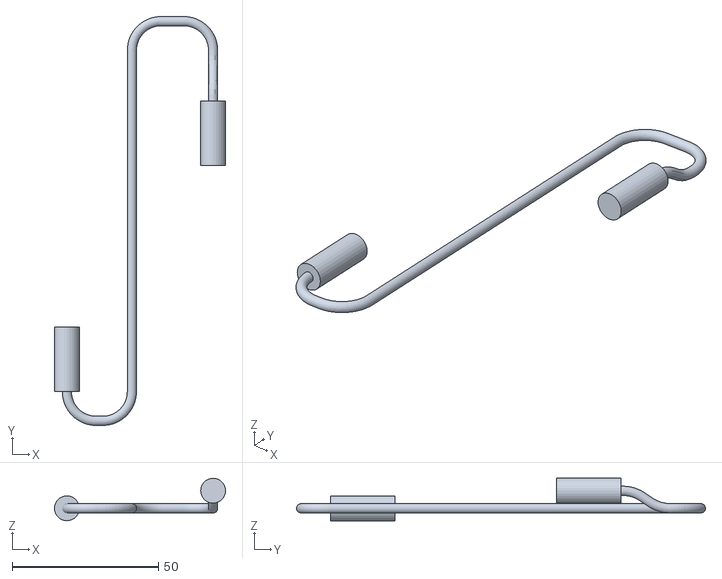
[picture p83: CAD file, 2026-08-27]
viewer/viewer_dc_cable.stl
58.4 x 139.7 x 14.5
