aeolyus/ha-green-poe-scad/viewer/variants/stacked_center/viewer_retention_corner_gate.stl

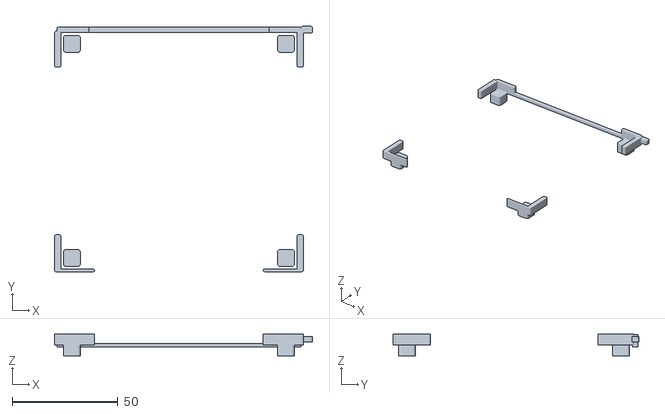
[picture p84: CAD file, 2026-08-28]
viewer/variants/stacked_center/viewer_retention_corner_gate.stl
121.8 x 115.9 x 10.3
