aeolyus/ha-green-poe-scad/viewer/viewer_retention_slide_latch.stl

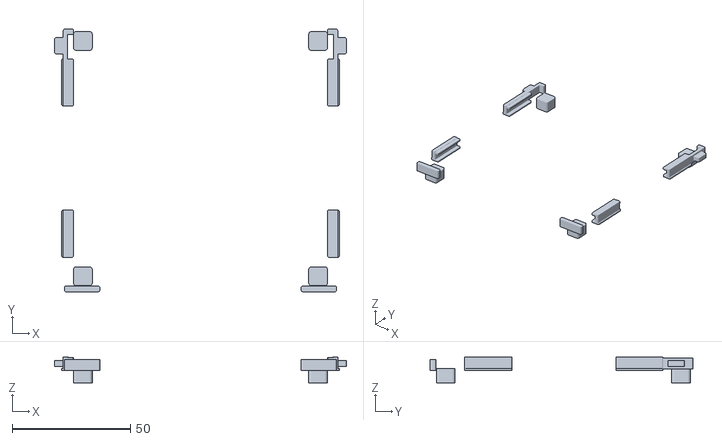
[picture p85: CAD file, 2026-08-27]
viewer/viewer_retention_slide_latch.stl
123.5 x 111.1 x 11.0
