aeolyus/ha-green-poe-scad/exports/led_fixed_window_kit_optional.3mf

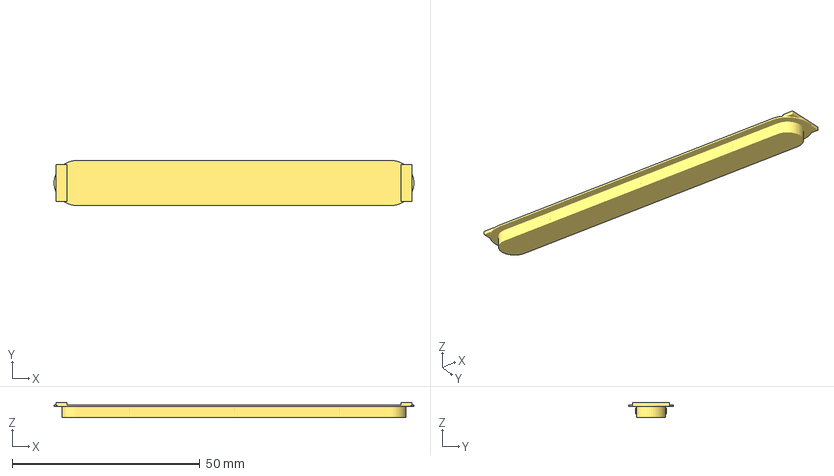
[picture p86: CAD file, 2026-08-27]
exports/led_fixed_window_kit_optional.3mf
96.0 x 12.0 x 4.05 mm
