aeolyus/ha-green-poe-scad/viewer/viewer_mount_without_green_tray.stl

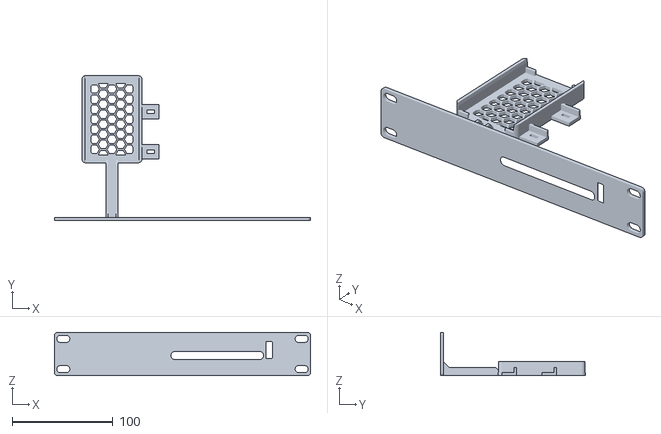
[picture p87: CAD file, 2026-08-27]
viewer/viewer_mount_without_green_tray.stl
254.0 x 143.7 x 43.0
