aeolyus/ha-green-poe-scad/viewer/variants/stacked_center/viewer_retention_captive_strap.stl

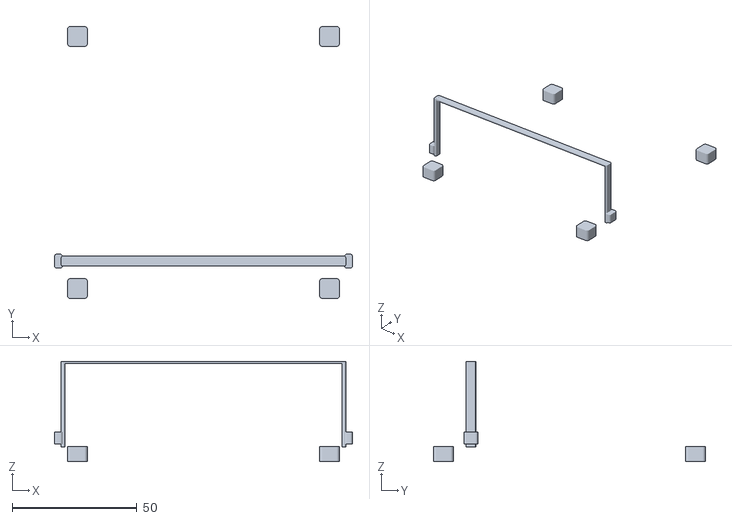
[picture p88: CAD file, 2026-08-28]
viewer/variants/stacked_center/viewer_retention_captive_strap.stl
119.5 x 109.1 x 40.3
