aeolyus/ha-green-poe-scad/exports/led_shutter_kit_front_ethernet_far_right_optional.3mf

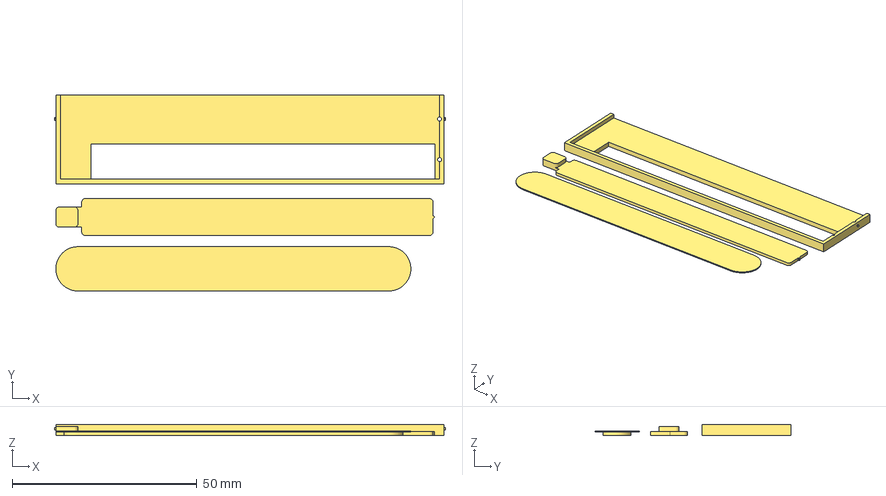
[picture p89: CAD file, 2026-08-27]
exports/led_shutter_kit_front_ethernet_far_right_optional.3mf
105.7 x 53.0 x 2.90 mm
