aeolyus/ha-green-poe-scad/viewer/variants/stacked_center/viewer_retention_x_cage.stl

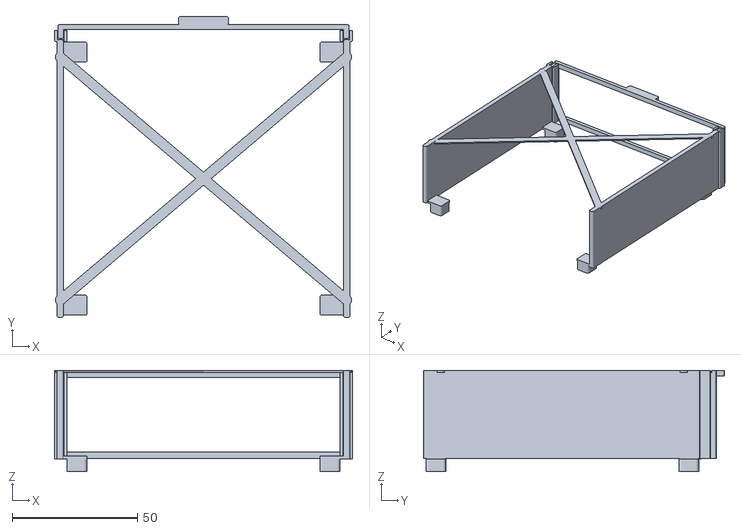
[picture p90: CAD file, 2026-08-28]
viewer/variants/stacked_center/viewer_retention_x_cage.stl
119.1 x 120.4 x 40.5
