aeolyus/ha-green-poe-scad/viewer/variants/stacked_center/viewer_retention_sled_gate.stl

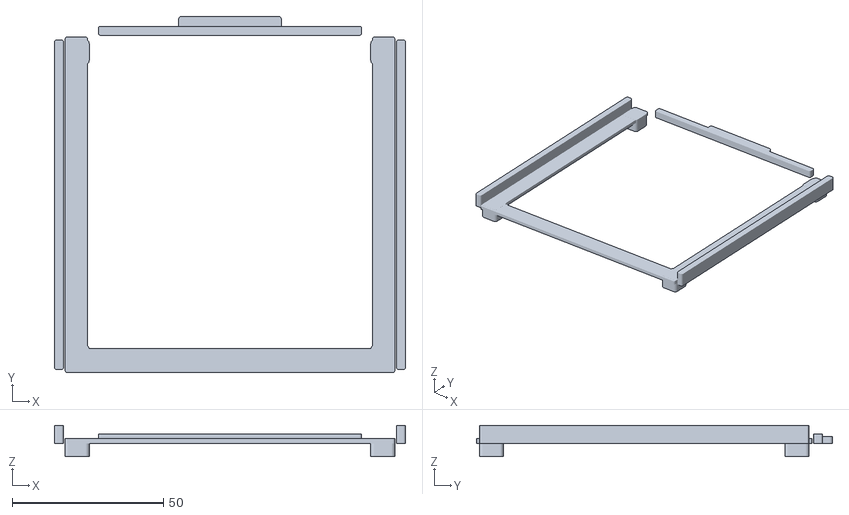
[picture p91: CAD file, 2026-08-28]
viewer/variants/stacked_center/viewer_retention_sled_gate.stl
116.1 x 117.9 x 10.4
