aeolyus/ha-green-poe-scad/exports/core_with_logo.stl

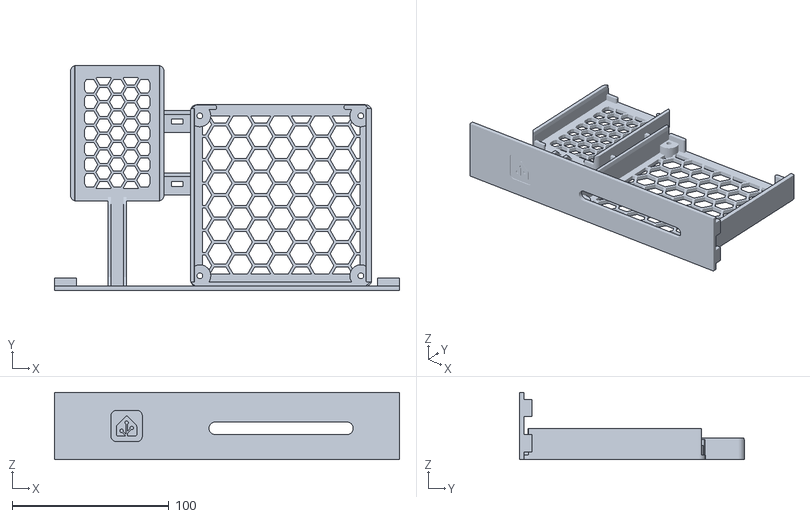
[picture p92: CAD file, 2026-08-27]
exports/core_with_logo.stl
220.0 x 143.7 x 43.0
