aeolyus/ha-green-poe-scad/viewer/viewer_splitter.stl

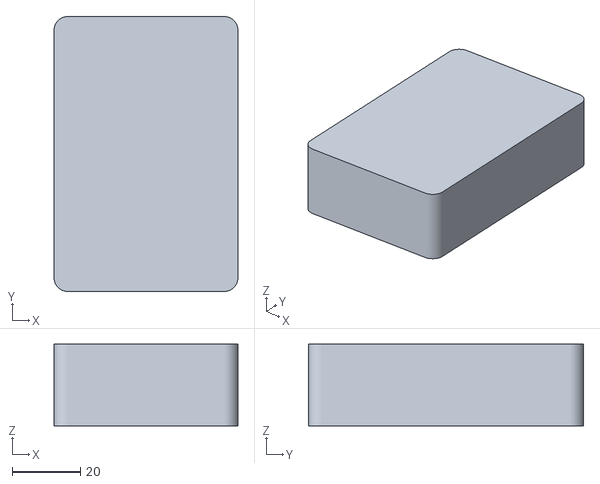
[picture p93: CAD file, 2026-08-27]
viewer/viewer_splitter.stl
54.0 x 80.8 x 24.0
