aeolyus/ha-green-poe-scad/viewer/viewer_fasteners.stl

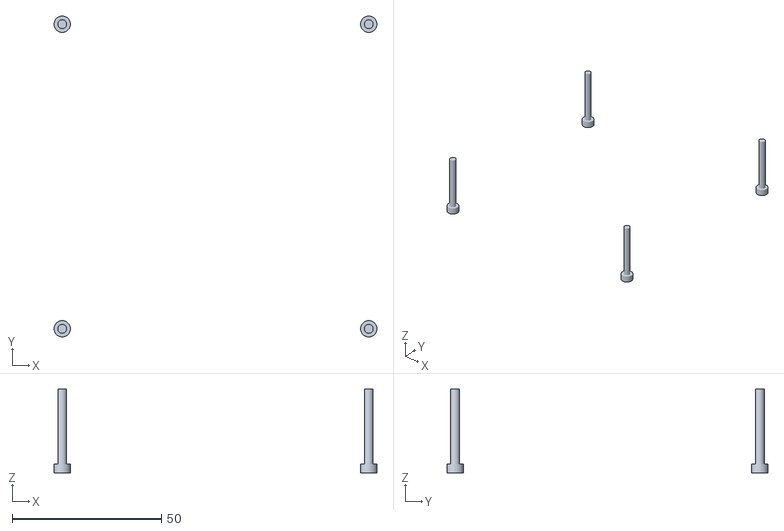
[picture p94: CAD file, 2026-08-27]
viewer/viewer_fasteners.stl
108.1 x 107.5 x 28.0
