aeolyus/ha-green-poe-scad/viewer/viewer_rulers.stl

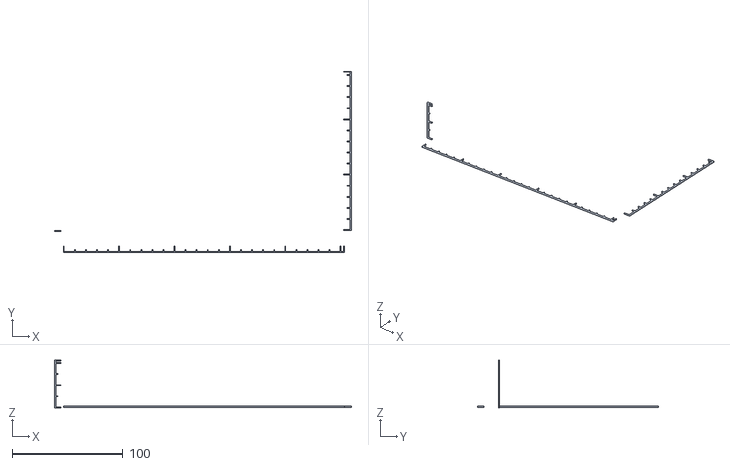
[picture p95: CAD file, 2026-08-27]
viewer/viewer_rulers.stl
268.2 x 163.7 x 43.0
