aeolyus/ha-green-poe-scad/exports/x2d_plate_front_ethernet_left.3mf

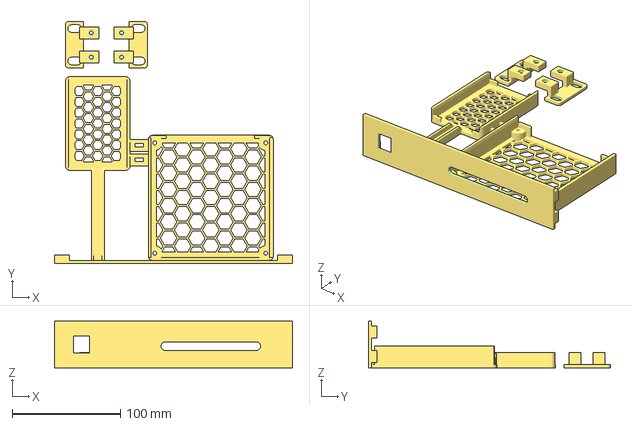
[picture p96: CAD file, 2026-08-27]
exports/x2d_plate_front_ethernet_left.3mf
220.0 x 223.7 x 43.0 mm
