aeolyus/ha-green-poe-scad/exports/core_front_ethernet_right.stl

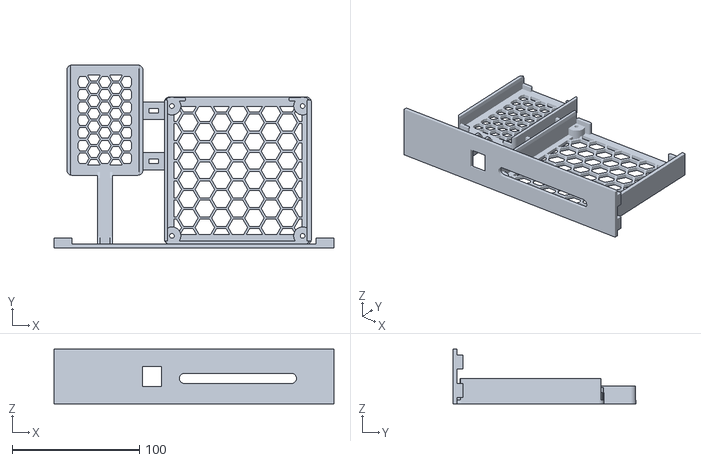
[picture p98: CAD file, 2026-08-27]
exports/core_front_ethernet_right.stl
220.0 x 143.7 x 43.0
