aeolyus/ha-green-poe-scad/exports/x2d_plate_with_shutter.3mf

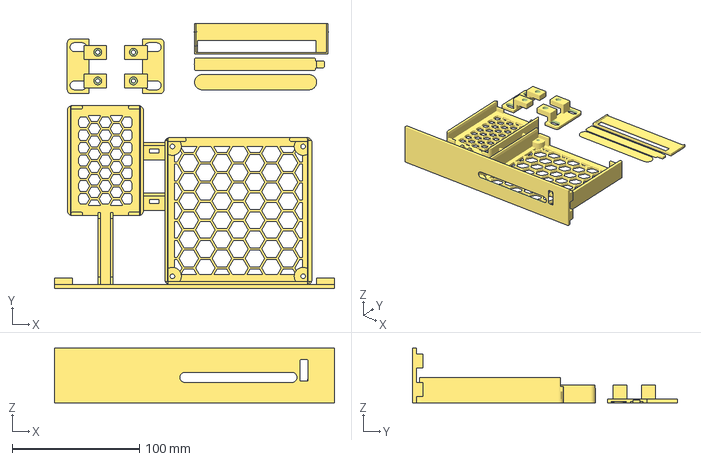
[picture p99: CAD file, 2026-08-27]
exports/x2d_plate_with_shutter.3mf
220.0 x 208.0 x 43.0 mm
