aeolyus/ha-green-poe-scad/renders/assembly_preview.png

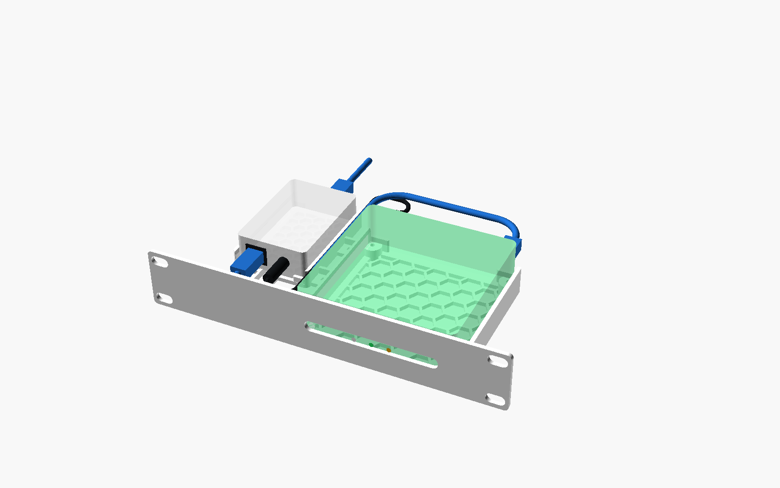
renders/assembly_preview.png
